magicamun/EnvNode/hardware/kicad/Sensors/SCT013Head/Lumberg_1503_09_Footprint.md

# Lumberg 1503 09 – SensorHead-Footprint

Quelle: https://cdn-reichelt.de/documents/datenblatt/C160/DS_1503_09.pdf (03/2007).
Draufsicht auf F.Cu, Stecköffnung nach -Y. Ursprung: Pad 1.
Das Hersteller-Bohrbild zeigt die Lötseite; X wurde für die Draufsicht gespiegelt.

| Pad | Funktion | X mm | Y mm | Langloch X × Y mm |
|---|---|---:|---:|---|
| 1 | Sleeve | 0 | 0 | 1,5 × 0,8 |
| 2 | Ring | -4,55 | 3,10 | 0,8 × 1,5 |
| 3 | Tip | 5,05 | 7,80 | 0,8 × 1,5 |
| 4 | Ring-Schaltkontakt (NC zu 2) | -4,00 | 11,00 | 1,5 × 0,8 |
| 5 | Tip-Schaltkontakt (NC zu 3) | 2,65 | 6,40 | 0,8 × 1,5 |

Durchkontaktierte Langlöcher gemäß Datenblatt, umlaufend 0,45 mm Kupferring.
Gehäuse 11,5 × 14,1 mm; Gewindehals nominell 3,5 mm lang und 6 mm Durchmesser.
F.Fab zeigt die nominelle Geometrie; F.CrtYd enthält 0,5 mm Reserve.
Keine Gehäusebohrung und kein Platinenkantenausschnitt werden automatisch erzeugt.
Kein 3D-Modell enthalten. Mutter/Freigängigkeit separat in der Gehäusekonstruktion berücksichtigen.
Vor Fertigung mechanische Passprobe mit Originalteil empfohlen.

Die Padnummern entsprechen dem Hersteller, nicht automatisch einem generischen KiCad-Audiosymbol.
Beim Symbol die Zuordnung 1=S, 2=R, 3=T, 4=RN, 5=TN beachten.
Den bestehenden zweipoligen J1 nicht ohne passende Pinzuordnung mit diesem fünfpoligen Footprint verknüpfen.
