magicamun/EnvNode/docs/site/sensors/sct013.md

# SCT013 und SCT013Head

!!! note "Entwicklungsstand / WIP"
    Der SCT013Head ist eine passive Aufbereitung für einen Stromwandler mit
    Spannungsausgang. Ein SCT013-Treiber ist in der gemeinsamen Firmware noch
    nicht registriert. Diese Seite ist keine fertige Aufbau- oder Kalibrieranleitung.

## Aufgabe und unterstützter Sensortyp

Der Head nimmt das Wechselspannungssignal eines SCT013 mit integrierter Bürde
und Spannungsausgang auf und verschiebt es in den positiven Messbereich des ESP32-ADC.
Die genaue SCT013-Ausführung, Nennstrom und Ausgangsspannung müssen zum Aufbau passen.
SCT013-Varianten mit reinem Stromausgang sind durch diesen Entwurf nicht abgedeckt.

Die kompakte Platine wird von einer verschraubten Lumberg-1503-09-Buchse getragen.
Das Pigtail zum Mainboard benötigt eine eigene Zugentlastung.

## Anschluss zum Mainboard

| Pin | Funktion |
| --- | --- |
| 1 | GND |
| 2 | Nicht verwendet; die angebotenen 5 V werden nicht genutzt |
| 3 | Aufbereitetes ADC-Signal |
| 4 | +3V3_SYS |

Das passt zur vierpoligen ADC-Portbelegung von Mini und Weather.
Verwende einen analogen Eingang und prüfe die tatsächliche Verdrahtung.

## Signalaufbereitung

Die aktuelle Entwurfsbeschreibung nennt R1 = R4 = 10 kΩ als Teiler relativ zur
Vorspannung VBIAS. R2/R3 bilden die Vorspannung aus der 3,3-V-Versorgung;
C2 stabilisiert sie. C1 = 10 nF liegt parallel zu R4.
Tip der Sensorbuchse führt über R1 zum ADC, Sleeve liegt an VBIAS.

Die Auslegung muss zum konkreten Spannungsausgang passen. Die Unterlagen enthalten
verschiedene Sensor-Ausgangspunkte; daraus ergibt sich keine universelle Stromkalibrierung.
Eine garantierte Überstromfestigkeit oder Schutzbeschaltung ist nicht nachgewiesen.

## Was vor einer Aufbauanleitung fehlt

- Konkrete SCT013-Ausführung und deren Ausgangsdaten festlegen.
- R1 in der Teileliste abgleichen: Der aktuelle Entwurf nennt 10 kΩ,
  der dokumentierte Artikelstand führt noch 1 kΩ.
- Schaltplan-/PCB-Zuordnung des ADC-Anschlusses und Bestückungsdruck abschließen.
- Buchse, Gehäusewand, Stecker und Zugentlastung mechanisch prüfen.
- Signalgrenzen, ADC-Abtastung, RMS-Auswertung und Kalibrierung am realen Aufbau prüfen.

Es gibt derzeit keine freigegebene PDF-Aufbauanleitung für den SCT013Head.
Historische Prüfnotizen mit widersprüchlichen Zwischenständen werden hier nicht
als aktuelle Fertigungsfreigabe übernommen.
