magicamun/EnvNode/docs/site/modules/index.md

# Erweiterungsmodule

Zum ersten Dokumentationsumfang gehören zwei Module:

| Modul | Aufgabe | Dokumentierter Stand |
| --- | --- | --- |
| [AnalogHydroPressure](analog-hydro-pressure/index.md) | Analoger Drucksensoranschluss und lokale 5-V-auf-24-V-Versorgung | Revision 0.5 |
| [DuoRelay](duo-relay/index.md) | Zwei über AUX_GPIO gesteuerte 5-V-Wechslerrelais | Revision 0.3 |

Die Produktseiten enthalten Verdrahtung, Bestückung, Inbetriebnahme und PDF-Anleitungen.
Wähle den Modulslot und die Firmware-Konfiguration passend zur tatsächlichen Hardware.
Die optionale EEPROM-Identifikation allein aktiviert keinen Modultreiber.
