magicamun/EnvNode/docs/site/kits/index.md

# Bausätze und Aufbau

Für den ersten Aufbau beginnt die Dokumentation mit [EnvNode Mini](../mainboards/mini/index.md).
Die revisionsbezogene Bestückungs- und Bring-up-Anleitung enthält die detaillierten
Montage- und Prüfabläufe.

## Sinnvolle Reihenfolge

1. Platinenrevision und dazugehörige Anleitung abgleichen.
2. Mainboard und Versorgungsbaustein nach Anleitung bestücken und prüfen.
3. Versorgung ohne Sensoren und Erweiterungsmodule kontrollieren.
4. Firmware und Boardprofil prüfen.
5. Einen unterstützten I²C-Sensor anschließen und eine erste Messung prüfen.
6. MQTT einrichten; weitere Module einzeln ergänzen.

Konkrete Kit-Lieferumfänge und Artikelzuordnungen werden erst nach Abgleich mit der
Teileliste ergänzt.
