magicamun/EnvNode/docs/site/mainboards/index.md

# Mainboards und Versorgung

| Baustein | Einordnung | Dokumentierter Stand |
| --- | --- | --- |
| [EnvNode Mini](mini/index.md) | Kompaktes Mainboard mit zwei Modulslots | Revision 0.8 |
| [EnvNode Weather / Weatherstation](weatherstation/index.md) | Mainboard mit einem Modulslot und zusätzlichen direkten Anschlüssen | Revision 0.2 |
| [ORing Power](oring-power/index.md) | Aufgelöteter Versorgungsbaustein für Mainboards | Anleitung 0.1; keine formale PCB-Revision |

Die Produktseiten enthalten Anschlüsse, Versorgung, Bestückung und erste Inbetriebnahme
sowie die zugehörigen PDF-Anleitungen. Revisionsangaben beziehen sich auf die
vorhandenen Unterlagen; gleiche sie mit deiner eingesetzten Platine ab.
