magicamun/EnvNode/hardware/kicad/Modules/FullSize/DuoRelay/Documentation/DuoRelay_Bestueckungs_und_Bringup_Rev0.2.pdf

ENVNODE · DUORELAY REV. 0.2

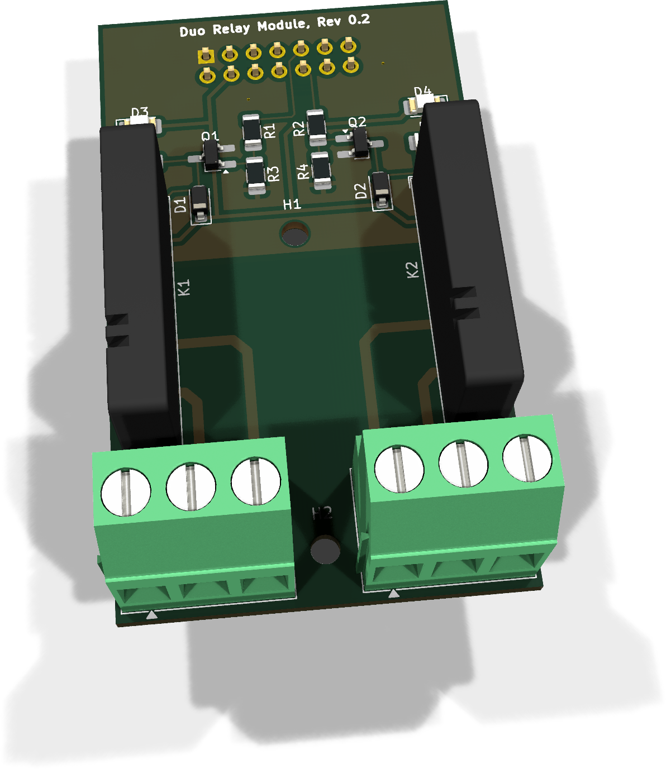
[picture p26: figure]

Bestückungs- und Bring-up-Anleitung · Entwurf · 1

ENVNODE DUORELAY

# Bestückungs- und Bring-up-Anleitung

FullSize-Modul Revision 0.2 · Erster Entwurf · PCB-Arbeitsstand 2. September 2026

Geltungsbereich: Diese Anleitung gilt für den aktuellen KiCad-Arbeitsstand des DuoRelay FullSize-Moduls und die Zuordnung im EnvNode-Artikelstamm. Sie beschreibt Handbestückung, Sichtprüfung und Erstinbetriebnahme mit Kleinspannung.

Dokumentstand: 2. September 2026

# 1. Teile und Vorbereitung

### 1.1 Elektronische Bestückung

Ref. | Anz. | Value / elektrische Daten | EnvNode-Part | Gehäuse / Footprint
D1, D2 | 2 | 1N4148W Freilaufdiode | ENP-00033 | SOD-123
D3, D4 | 2 | LED rot, KP-3216SURC | ENP-00064 | 1206 / 3216 Metric
R1, R2 | 2 | 1 kΩ, 1 %, 250 mW | ENP-00036 | 1206 / 3216 Metric
R3, R4 | 2 | 100 kΩ, 0,1 %, 250 mW | ENP-00016 | 1206 / 3216 Metric
R5, R6 | 2 | 1,5 kΩ, 1 %, 250 mW | ENP-00065 | 1206 / 3216 Metric
Q1, Q2 | 2 | BC817 NPN | ENP-00035 | SOT-23 Handsoldering
K1, K2 | 2 | Finder 34.51, 5-V-Spule, 1 Wechsler | ENP-00023 | Relay SPDT Finder 34.51
J3, J4 | 2 | Schraubklemme 1x3, 5,08 mm | ENP-00034 | Phoenix MKDS-3 horizontal
J1 | 1 | Stiftleiste 2x7, Bottom-Mount | ENP-00059 | EnvNode Bottom-Footprint
U1 | 1 | 24AA025E64T-I/OT Identifikations-EEPROM | ENP-00024 | SOT-23-6, derzeit DNP
C1 | 1 | 100 nF, X7R | ENP-00006 | 1206, derzeit DNP
PCB | 1 | DuoRelay FullSize Rev. 0.2 | ENP-00066 | 38,00 x 64,00 mm

DNP-Stand: U1 und C1 sind im aktuellen Kit als nicht zu bestücken geführt. Die Relaisfunktion arbeitet ohne EEPROM. Für spätere automatische Modulerkennung können beide Positionen nach Freigabe bestückt und U1 provisioniert werden.

### 1.2 Orientierung und Sicherheit

□ D1/D2: Kathodenmarkierung am Bauteil mit dem PCB-Aufdruck abgleichen.

□ D3/D4: LED-Polarität anhand Pin-1-/Kathodenmarkierung kontrollieren.

□ Q1/Q2: SOT-23-Lage und Pin-1-Markierung nicht spiegeln.

□ J1 wird von der Modulunterseite bestückt. Pin 1 ist am Footprint und am quadratischen Pad erkennbar.

□ K1/K2 und J3/J4 müssen plan aufliegen; erst einen Pin fixieren, Lage korrigieren, danach vollständig löten.

□ H1/H2 sind 2,7-mm-Bohrungen für M2,5-Hardware. Abstandshalter dürfen keine Leiterbahnen oder Lötstellen berühren.

Sicherheitsgrenze: Die vorhandenen Abstände und Relaisdaten sind keine Freigabe für Netzspannung. Klemmen, Sicherung, Gehäuse, Berührungsschutz, Lastart, Verschmutzungsgrad und Produktnorm müssen für die konkrete Anwendung bewertet werden. Der erste Bring-up erfolgt ausschließlich mit sicherer Kleinspannung.

### 1.3 Benötigte Hilfsmittel

□ Feinlötkolben, geeignetes Lot und Flussmittel; Vergrößerung für SOT-23 und SOD-123.

□ Multimeter mit Widerstands-, Dioden- und Durchgangsmessung.

□ Strombegrenztes 5-V-Labornetzteil und zwei ungefährliche Kleinspannungs-Testlasten.

□ Geeignetes EnvNode-Mainboard oder Prüfvorrichtung für AUX_GPIO1 und AUX_GPIO2.

# 2. Bestückungsübersicht

Bestückungsseite: J1 liegt oben, die beiden Treiberkanäle sind spiegelbildlich aufgebaut. Kanal 1 befindet sich links mit Q1, D1, D3, K1 und J3; Kanal 2 rechts mit Q2, D2, D4, K2 und J4.

Die Kontaktbezeichnungen sind am unteren Rand aufgedruckt. Vor externer Verdrahtung NO, COM und NC zusätzlich mit der Durchgangsmessung verifizieren.

### 2.1 Unterseite und Modulstecker

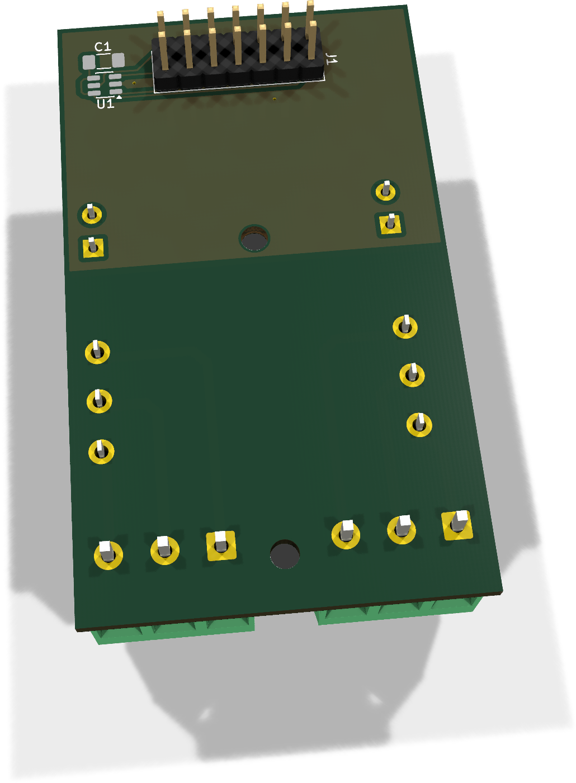
[picture p27: figure]

Unterseitenansicht: J1 sowie die optionalen Positionen U1/C1 liegen auf dieser Seite. Die Relais- und Klemmenanschlüsse erscheinen in der Ansicht gespiegelt.

Wichtig: J1 ist ein Bottom-Mount-Stecker. Nicht durch einen normalen, von oben bestückten 2x7-Header ersetzen; Pinreihenfolge und mechanische Einbaulage wären sonst falsch.

# 3. Empfohlene Löt-Reihenfolge

### 1. Widerstände

R1/R2 = 1 kΩ, R3/R4 = 100 kΩ und R5/R6 = 1,5 kΩ bestücken. Werte kanalweise gegenprüfen.

### 2. Dioden und LEDs

D1/D2 sowie D3/D4 polaritätsrichtig montieren. Nach jedem Kanal Diodentest durchführen.

### 3. Transistoren

Q1/Q2 ausrichten, zunächst einen Pin fixieren und anschließend alle Pins sauber benetzen.

### 4. Optional U1/C1

Im aktuellen Rev.-0.2-Kit DNP lassen. Nur gemeinsam und nach Freigabe der Identifikationsfunktion bestücken.

### 5. Bottom-Mount J1

Stecker von der Unterseite einsetzen. Mit einer Buchse oder Vorrichtung rechtwinklig halten und über Kreuz anlöten.

### 6. Relais K1/K2

Plan auf die Oberseite setzen. Zuerst je zwei weit auseinanderliegende Pins fixieren, Sitz prüfen, dann fertig löten.

### 7. Klemmen J3/J4

Öffnung nach außen ausrichten, plan auflegen und mechanisch belastbare THT-Lötstellen herstellen.

### 8. Reinigung und Sichtprüfung

Flussmittelreste entfernen, Kontaktbereich auf Fremdkörper prüfen und alle Lötstellen unter Vergrößerung abnehmen.

# 4. Anschlussbelegung

### 4.1 EnvNode-Modulstecker J1

Pin | Netz | Verwendung
1 | GND | Treiberreferenz
2 | +3V3_SYS | optional U1; A1 fest HIGH
3 | EEPROM_A0 | Slotabhängige U1-Adresse
4 | +5V | Relais- und LED-Versorgung
5 / 6 | I2C0_SDA / SCL | optional U1
7 / 8 | I2C1 | nicht verwendet
9 | AUX_GPIO1 | Relaiskanal 1
10 | AUX_GPIO2 | Relaiskanal 2
11-14 | SPI | nicht verwendet

Die Treibereingänge besitzen je 100 kΩ Pull-down. Beide Relais müssen während Reset, Boot und bei abgezogenem Controller sicher abgefallen bleiben.

### 4.2 Relaiskontakte J3/J4

Kanal | Klemme | Kontaktfolge laut Aufdruck
1 | J3 | NO - COM - NC
2 | J4 | NC - COM - NO

Die beiden Klemmen sind gegenüberliegend orientiert. Kontaktfolge daher nicht pauschal übertragen, sondern Aufdruck und Durchgangsmessung verwenden.

# 5. Prüfungen ohne Versorgung

□ Sichtprüfung aller Lötstellen, Leiterplattenkanten und Abstände bestanden.

□ Kein niederohmiger Kurzschluss zwischen +5 V und GND sowie zwischen +3V3_SYS und GND.

□ Q1/Q2 und D1/D2 in plausibler Diodenrichtung; keine Brücke an den SOT-23-Pins.

□ J1 von der Unterseite bestückt, Pin 1 korrekt, Stecker rechtwinklig und vollständig verlötet.

□ K1/K2 und J3/J4 plan aufliegend; keine kalten oder gerissenen THT-Lötstellen.

□ Relais im Ruhezustand: COM-NC niederohmig, COM-NO offen; beide Kanäle getrennt prüfen.

□ Zwischen Kontaktkreis und GND, +5 V, +3V3_SYS sowie GPIOs kein Durchgang.

□ U1/C1 entsprechend Fertigungsauftrag beide DNP oder beide freigegeben bestückt.

Bei jeder unerwarteten Verbindung zwischen Relaiskontaktseite und SELV-Steuerseite darf das Modul nicht eingeschaltet werden.

# 6. Erstinbetriebnahme

Schritt | Aktion / Erwartung
1 | Ohne externe Lasten und ausschließlich mit 5 V Kleinspannung starten. Strombegrenzung zunächst auf etwa 150 mA einstellen.
2 | Beide AUX_GPIO-Eingänge LOW halten. K1/K2 müssen abgefallen und D3/D4 aus sein.
3 | AUX_GPIO1 auf HIGH setzen: D3 leuchtet, K1 zieht hörbar an; AUX_GPIO2 bleibt aus.
4 | An J3 prüfen: COM-NO geschlossen, COM-NC offen. GPIO1 wieder LOW; Ruhezustand muss zurückkehren.
5 | AUX_GPIO2 entsprechend prüfen: D4, K2 und J4; Kanal 1 muss unbeeinflusst bleiben.
6 | Beide Kanäle kurz gleichzeitig einschalten; 5-V-Spannung und Stromaufnahme dokumentieren.

### 6.1 Funktions- und Belastungstest

□ Für die erste Kontaktprüfung nur eine berührungssichere Kleinspannungs-Testlast verwenden.

□ Jeden Kanal mindestens zehnmal schalten; LED, Relaisgeräusch und Kontaktzustand müssen konsistent sein.

□ Beide Kanäle gleichzeitig betätigen und Versorgungseinbruch am Modulstecker beobachten.

□ Kontaktwiderstand und Erwärmung bei der vorgesehenen Last gesondert qualifizieren.

□ Induktive, kapazitive und motorische Lasten benötigen eine anwendungsabhängige Schutzbeschaltung und Absicherung.

# 7. Messprotokoll

Prüfpunkt | Soll | Messwert | Bestanden | Bemerkung
+5 V am J1 | 4,75 bis 5,25 V
Ruhestrom, beide aus | dokumentieren
GPIO1 LOW / HIGH | K1 aus / ein
GPIO2 LOW / HIGH | K2 aus / ein
D3 / D4 | folgen K1 / K2
J3 Ruhe / aktiv | NC / NO korrekt
J4 Ruhe / aktiv | NC / NO korrekt
Beide Relais aktiv | 5 V stabil
Isolation Kontakt/SELV | kein Durchgang

# 8. Fehlerbilder

Beobachtung | Zuerst prüfen
Relais bleibt aus | +5 V an J1, AUX_GPIO-Pegel, R1/R2, Q1/Q2, Spule K1/K2 und Freilaufdiode.
LED leuchtet, Relais schaltet nicht | 5-V-Spannung unter Last, Spulenanschlüsse, Relais-Lötstellen und Spulenwiderstand.
Relais zieht beim Booten an | 100-kΩ-Pull-down R3/R4, GPIO-Konfiguration und Pinbelegung des verwendeten Slots.
Kontaktzustand vertauscht | Klemmenorientierung beachten: J3 und J4 tragen spiegelbildliche Aufdrucke; COM per Durchgang finden.
Hoher Strom / Erwärmung | Sofort ausschalten; D1/D2, Q1/Q2, Lötbrücken und Relais-Spulen prüfen.
Kanal beeinflusst den anderen | Gemeinsame 5-V-Versorgung, GPIO-Zuordnung, Lötbrücke zwischen den Treiberstufen.
U1 nicht erreichbar | Nur relevant, wenn bestückt: 3,3 V, I2C0, A0/A1, Orientierung, Adresse 0x52/0x53.

Fertigungsreife: Der elektrische und mechanische Stand ist für einen Rev.-0.2-Prototypenlauf plausibel. Vor Serien- oder Netzspannungsfreigabe fehlen weiterhin eine konkrete Klemmen-MPN, Lastqualifikation und anwendungsbezogene Sicherheitsbewertung.

# 9. Revisionsnachweis

Quelle | SHA-256
DuoRelay.kicad_pcb | 242f9711c18cf81b858417ce0f0d68c631eef2593229de874035f0864615322a
DuoRelay.kicad_sch | 8d009b299b0227dc91bdb96572533ef9922993829f7346a84a8630300917435b
DuoRelay.kicad_pro | 4a3a8a0ed6be982b91e17260304250d8a5bfeda32ea36c9a860300edd74c057f
README.md | a8fd0f2843a57bf01c0c8512cdc5afea1712142397578280fab4029cf7853337
EnvNode_Parts.xlsx | bca95cb81872b41eca7a18517cb41fc68700cc3a1cb6595b4e2c0744d4d927c3

Prüfbasis: PCB-Titelblock Rev. 0.2, Datum 2026-08-29. ERC am 2. September 2026: 0 Fehler und 9 dokumentierte Warnungen. Der KiCad-PCB-Stand und die Gerber-Daten waren bereits vorhanden; die fertigungsspezifische Freigabe bleibt Aufgabe des jeweiligen Auftrags.
