magicamun/EnvNode/hardware/kicad/Sensors/RainDetectorHead/RainDetectorHead.kicad_pcb

## KiCad design hardware/kicad/Sensors/RainDetectorHead/RainDetectorHead.kicad_pcb (2026-09-15)

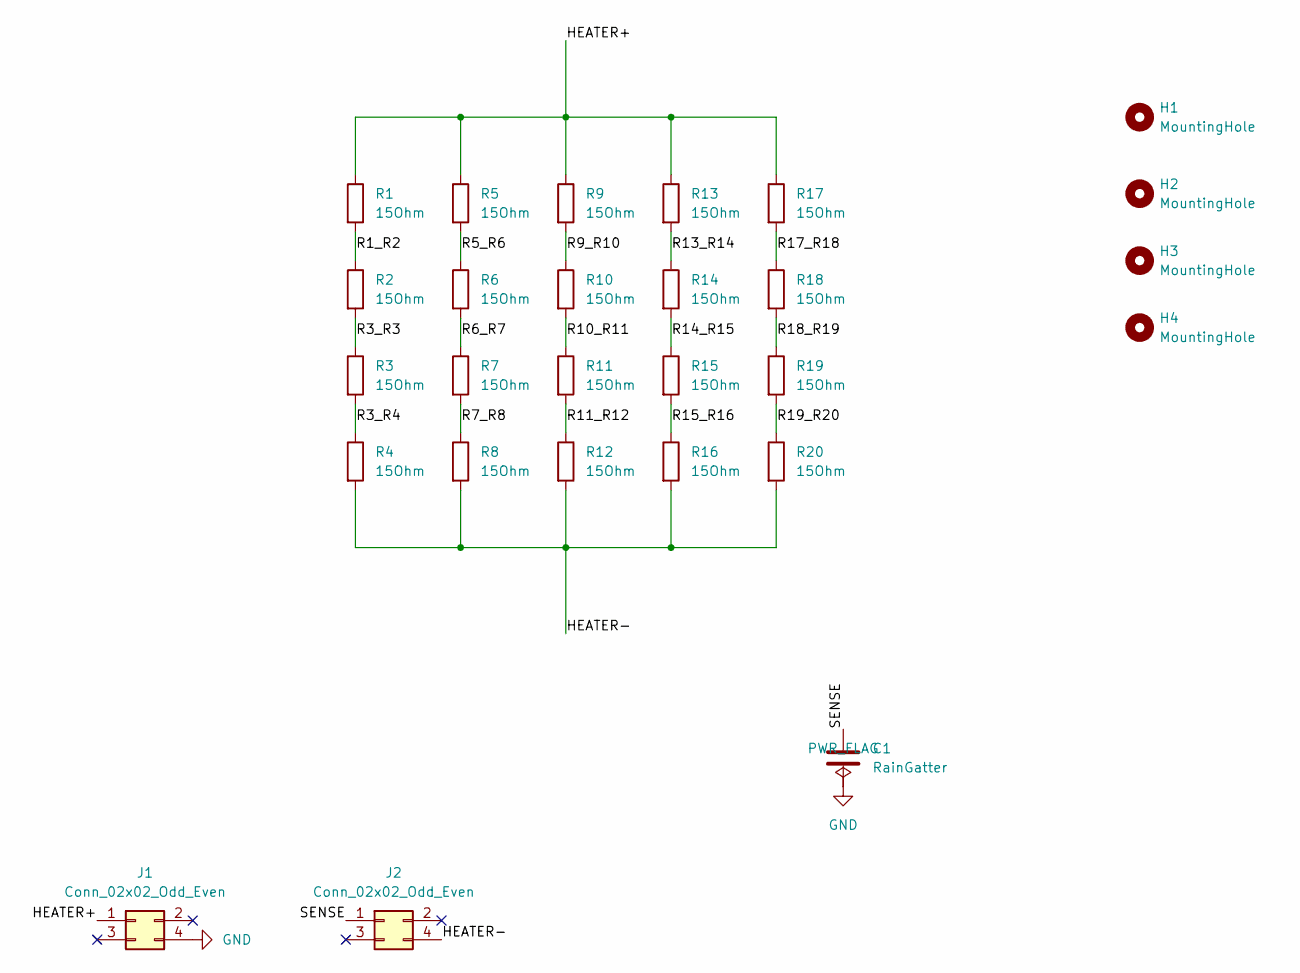
[picture p57: schematic RainDetectorHead.kicad_sch]

Parts:
C1: RainGatter; RainDetector_Interdigitated_48.86x37.25mm_P0.51mm
H1, H2, H3, H4: MountingHole; MountingHole_3.2mm_M3
J1, J2: Conn_02x02_Odd_Even; PinHeader_2x02_P2.54mm_Vertical_SMD
R1, R2, R3, R4, R5, R6, R7, R8, R9, R10, R11, R12, R13, R14, R15, R16, R17, R18, R19, R20: 15Ohm; R_1206_3216Metric_Pad1.30x1.75mm_HandSolder

Connections:
/HEATER+: J1.1, R1.1, R5.1, R9.1, R13.1, R17.1
/HEATER-: J2.4, R4.2, R8.2, R12.2, R16.2, R20.2
/R1_R2: R1.2, R2.1
/R3_R3: R2.2, R3.1
/R3_R4: R3.2, R4.1
/R5_R6: R5.2, R6.1
/R6_R7: R6.2, R7.1
/R7_R8: R7.2, R8.1
/R9_R10: R9.2, R10.1
/R10_R11: R10.2, R11.1
/R11_R12: R11.2, R12.1
/R13_R14: R13.2, R14.1
/R14_R15: R14.2, R15.1
/R15_R16: R15.2, R16.1
/R17_R18: R17.2, R18.1
/R18_R19: R18.2, R19.1
/R19_R20: R19.2, R20.1
/SENSE: C1.1, J2.1
GND: C1.2, J1.4

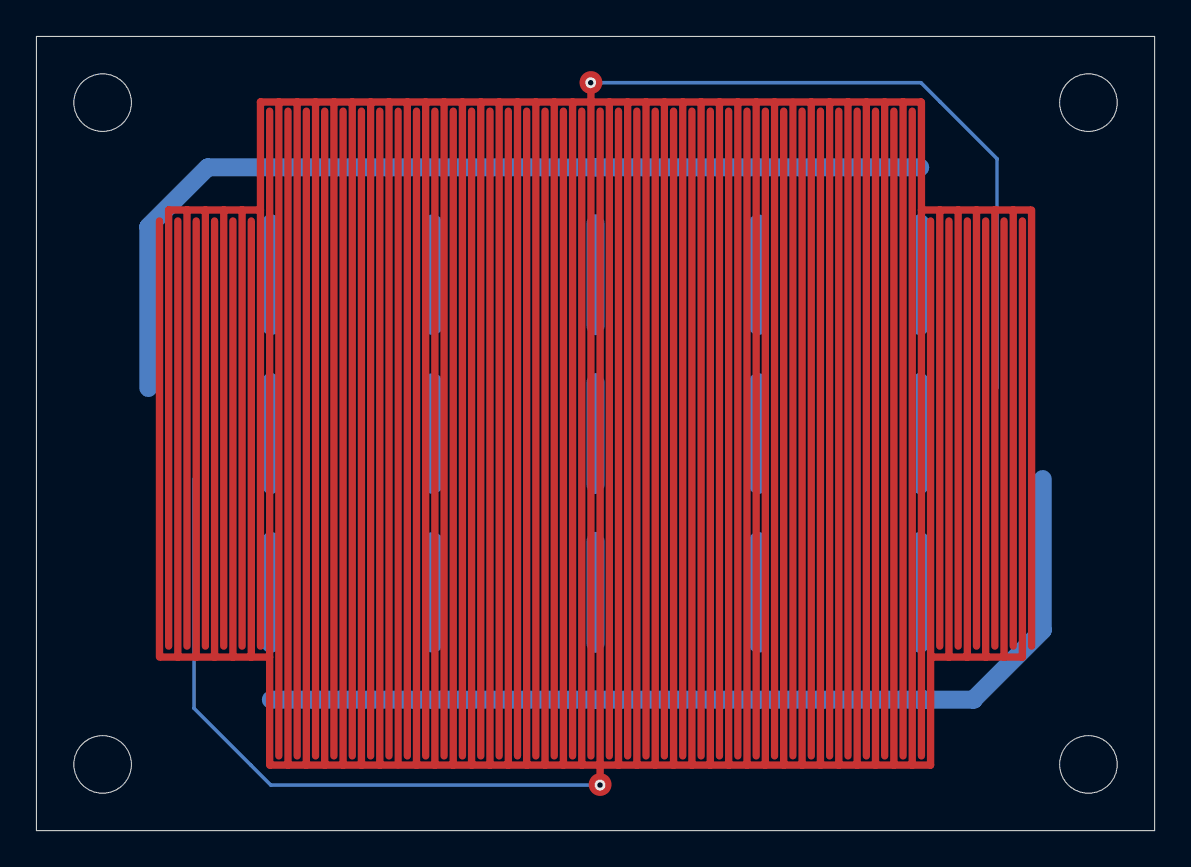
[picture p58: board RainDetectorHead.kicad_pcb from above]

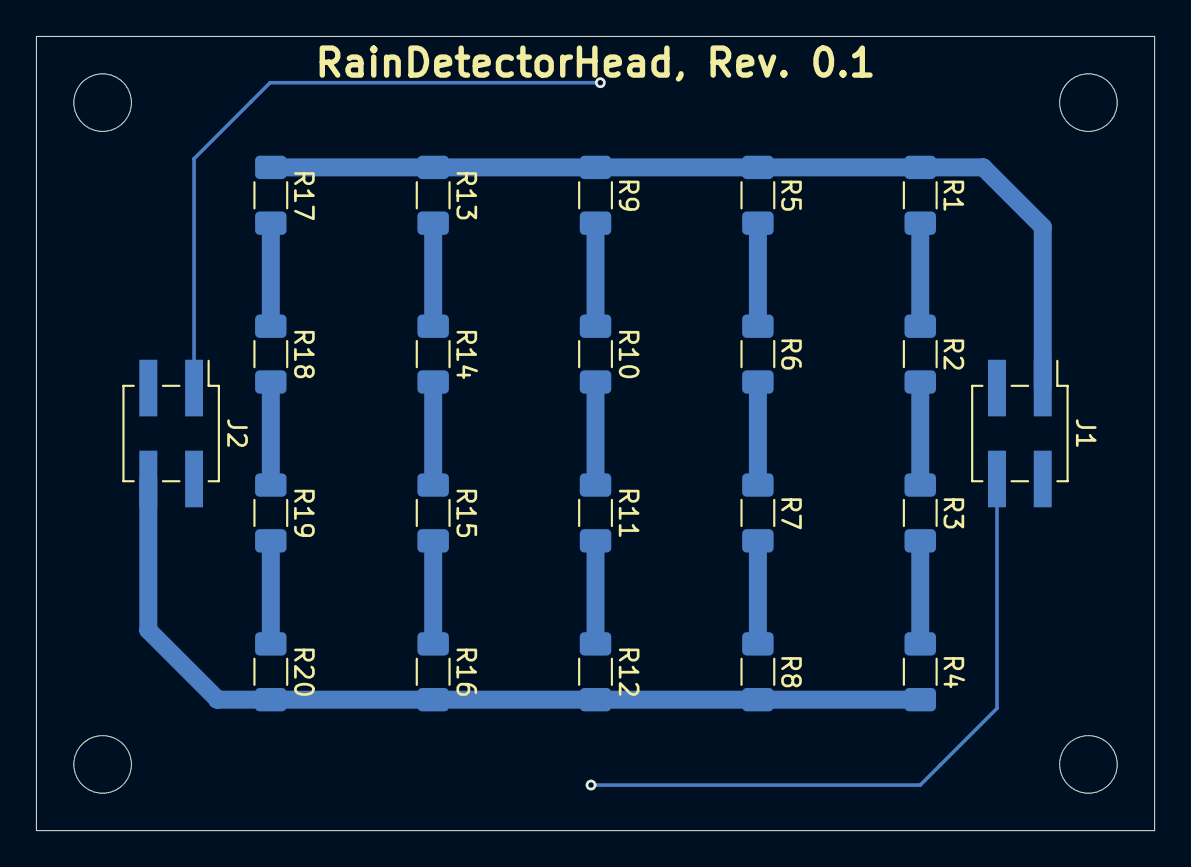
[picture p59: board RainDetectorHead.kicad_pcb from below]

Board: 2 copper layers, 62.1 x 44.1 mm, 27 parts (22 on the bottom side), 19 nets.
