magicamun/EnvNode/hardware/kicad/Sensors/RainDetectorController/RainDetectorController.kicad_pcb

## KiCad design hardware/kicad/Sensors/RainDetectorController/RainDetectorController.kicad_pcb (2026-09-15)

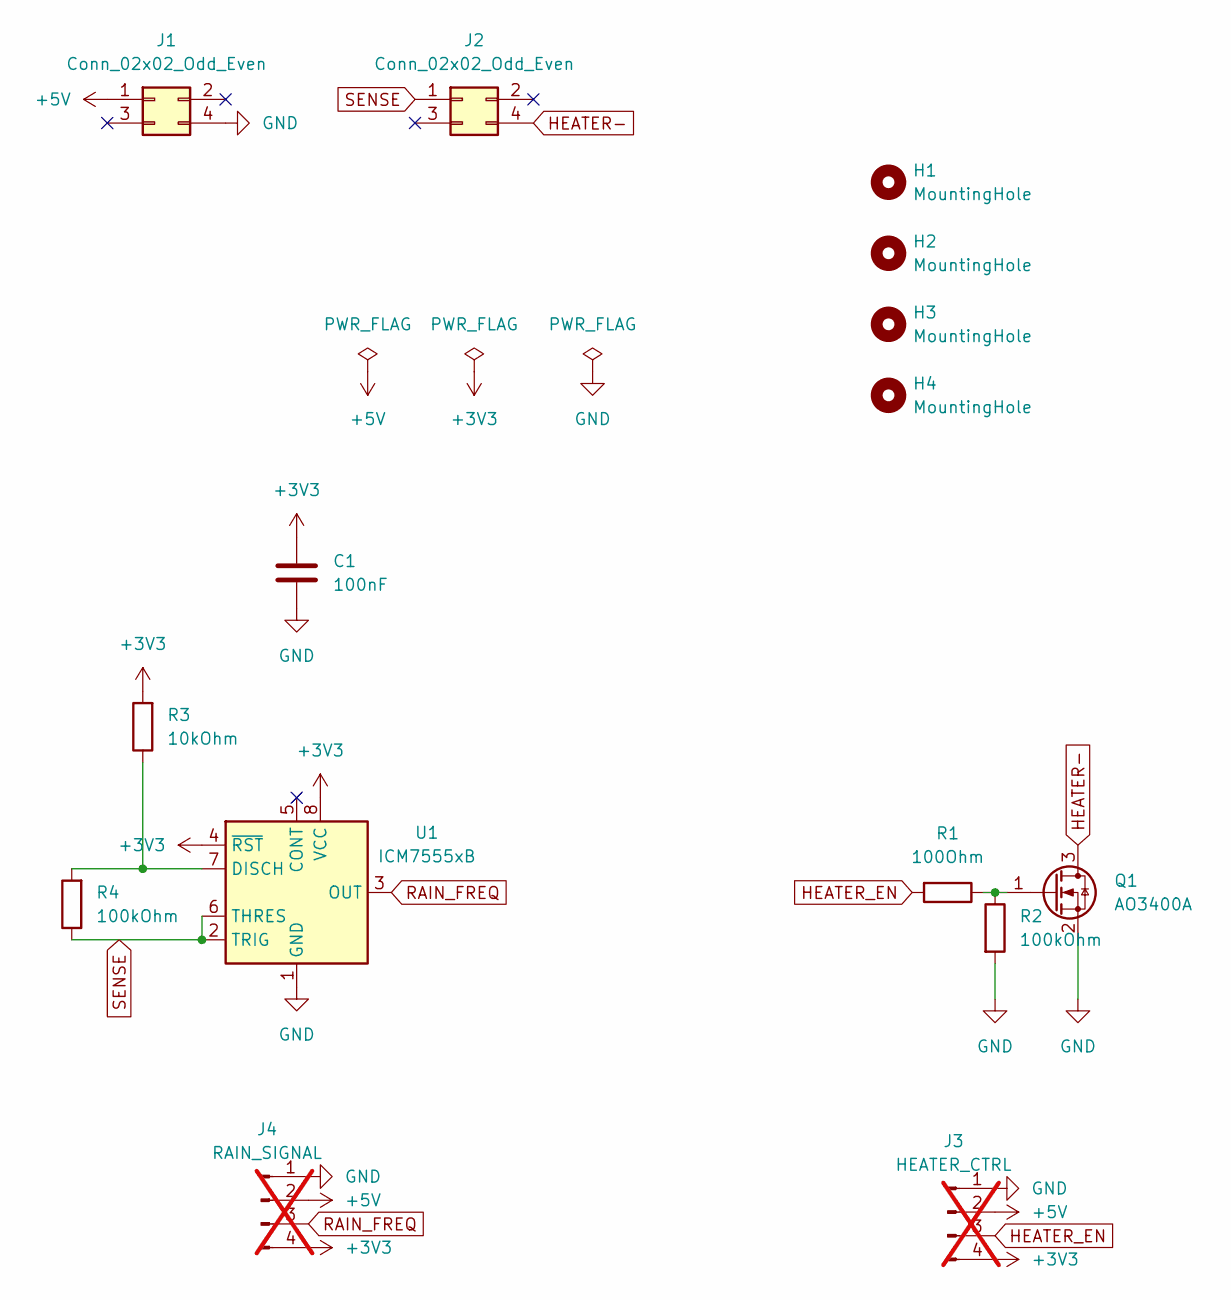
[picture p60: schematic RainDetectorController.kicad_sch]

Parts:
C1: 100nF; C_1206_3216Metric_Pad1.33x1.80mm_HandSolder
H1, H2, H3, H4: MountingHole; MountingHole_3.2mm_M3
J1, J2: Conn_02x02_Odd_Even; PinSocket_2x02_P2.54mm_Vertical
J3: HEATER_CTRL; PinHeader_1x04_P2.54mm_Vertical; not fitted
J4: RAIN_SIGNAL; PinHeader_1x04_P2.54mm_Vertical; not fitted
Q1: AO3400A; SOT-23
R1: 100Ohm; R_1206_3216Metric_Pad1.30x1.75mm_HandSolder
R2, R4: 100kOhm; R_1206_3216Metric_Pad1.30x1.75mm_HandSolder
R3: 10kOhm; R_1206_3216Metric_Pad1.30x1.75mm_HandSolder
U1: ICM7555xB; SOIC-8_3.9x4.9mm_P1.27mm

Connections:
+3V3: C1.1, J3.4, J4.4, R3.2, U1.4 (~RST), U1.8 (VCC)
+5V: J1.1, J3.2, J4.2
GND: C1.2, J1.4, J3.1, J4.1, Q1.2 (S), R2.2, U1.1 (GND)
HEATER-: J2.4, Q1.3 (D)
HEATER_EN: J3.3, R1.2
unnamed: Q1.1 (G), R1.1, R2.1
unnamed: R3.1, R4.2, U1.7 (DISCH)
RAIN_FREQ: J4.3, U1.3 (OUT)
SENSE: J2.1, R4.1, U1.2 (TRIG), U1.6 (THRES)

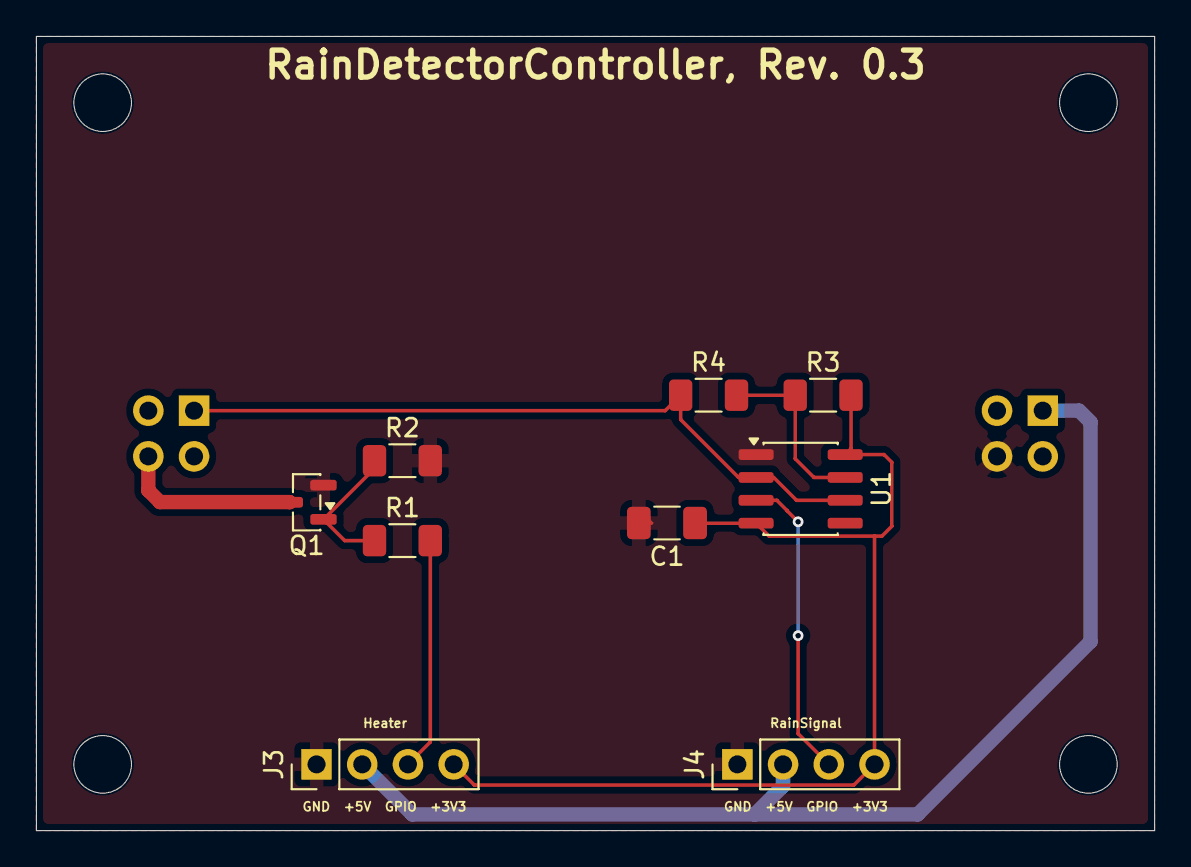
[picture p61: board RainDetectorController.kicad_pcb from above]

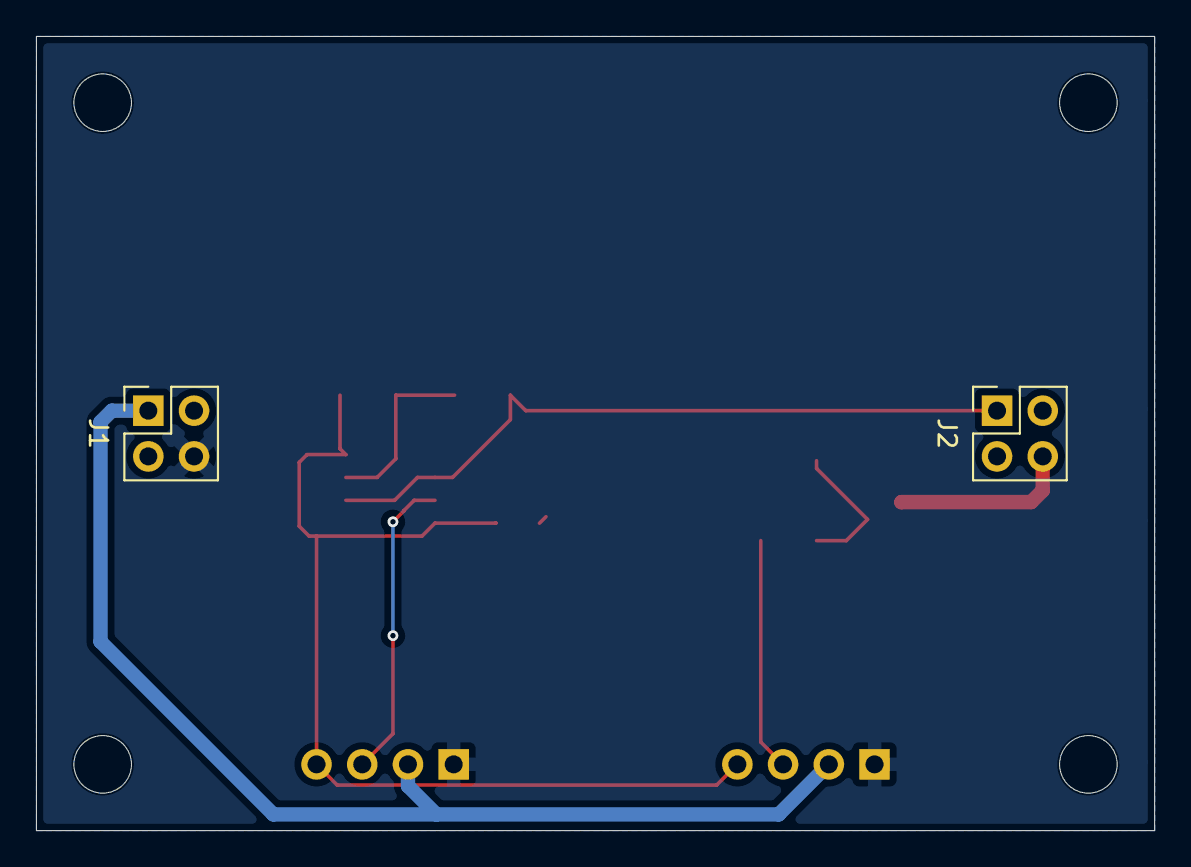
[picture p62: board RainDetectorController.kicad_pcb from below]

Board: 2 copper layers, 62.1 x 44.1 mm, 15 parts (2 on the bottom side), 9 nets.
