magicamun/EnvNode/hardware/kicad/Modules/HalfSize/I2C Carrier HalfSize/I2C Carrier HalfSize.kicad_pcb

## KiCad design hardware/kicad/Modules/HalfSize/I2C Carrier HalfSize/I2C Carrier HalfSize.kicad_pcb (2026-09-08)

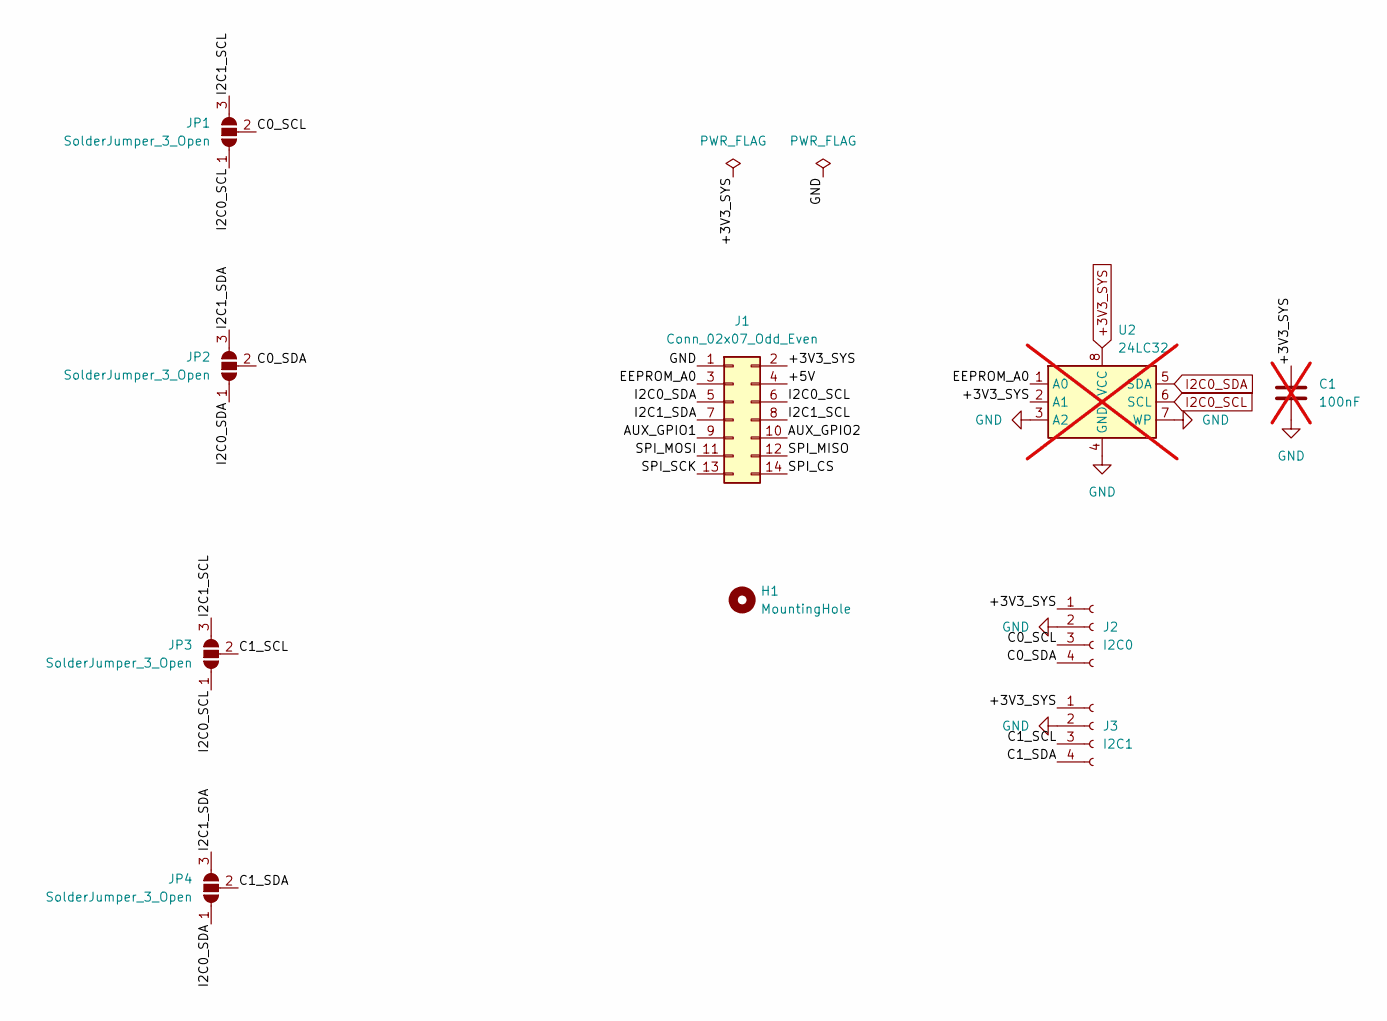
[picture p63: schematic I2C Carrier HalfSize.kicad_sch]

Parts:
C1: 100nF; C_1206_3216Metric_Pad1.33x1.80mm_HandSolder; not fitted
H1: MountingHole; MountingHole_2.7mm_M2.5_DIN965
J1: Conn_02x07_Odd_Even; PinHeader_2x07_P2.54mm_Vertical_Bottom
J2: I2C0; PinSocket_1x04_P2.54mm_Vertical
J3: I2C1; PinSocket_1x04_P2.54mm_Vertical
JP1, JP2, JP3, JP4: SolderJumper_3_Open; SolderJumper-3_P1.3mm_Open_RoundedPad1.0x1.5mm
U2: 24LC32; SOIC-8_3.9x4.9mm_P1.27mm; not fitted

Connections:
+3V3_SYS: C1.1, J1.2, J2.1, J3.1, U2.2 (A1), U2.8 (VCC)
/+5V: J1.4
/AUX_GPIO1: J1.9
/AUX_GPIO2: J1.10
/C0_SCL: J2.3, JP1.2 (C)
/C0_SDA: J2.4, JP2.2 (C)
/C1_SCL: J3.3, JP3.2 (C)
/C1_SDA: J3.4, JP4.2 (C)
/EEPROM_A0: J1.3, U2.1 (A0)
/I2C1_SCL: J1.8, JP1.3 (B), JP3.3 (B)
/I2C1_SDA: J1.7, JP2.3 (B), JP4.3 (B)
/SPI_CS: J1.14
/SPI_MISO: J1.12
/SPI_MOSI: J1.11
/SPI_SCK: J1.13
GND: C1.2, J1.1, J2.2, J3.2, U2.3 (A2), U2.4 (GND), U2.7 (WP)
I2C0_SCL: J1.6, JP1.1 (A), JP3.1 (A), U2.6 (SCL)
I2C0_SDA: J1.5, JP2.1 (A), JP4.1 (A), U2.5 (SDA)

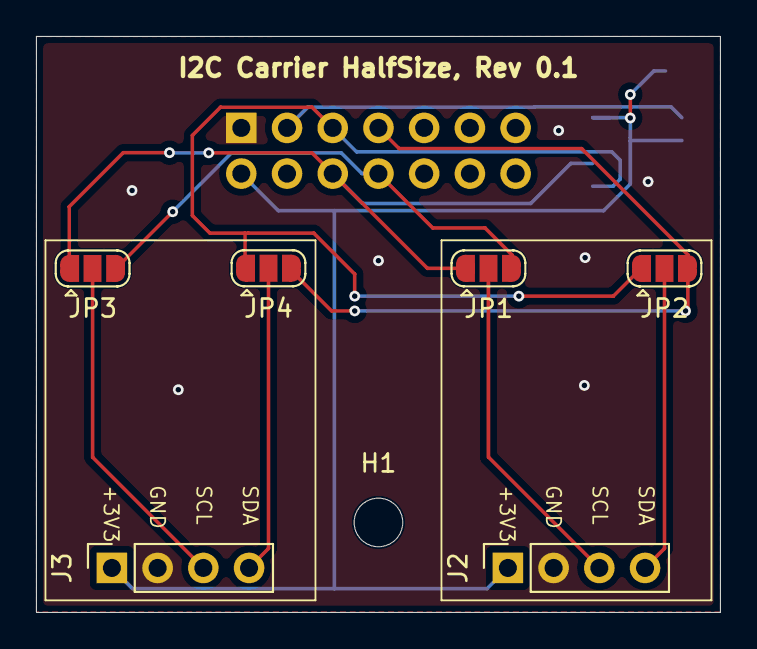
[picture p64: board I2C Carrier HalfSize.kicad_pcb from above]

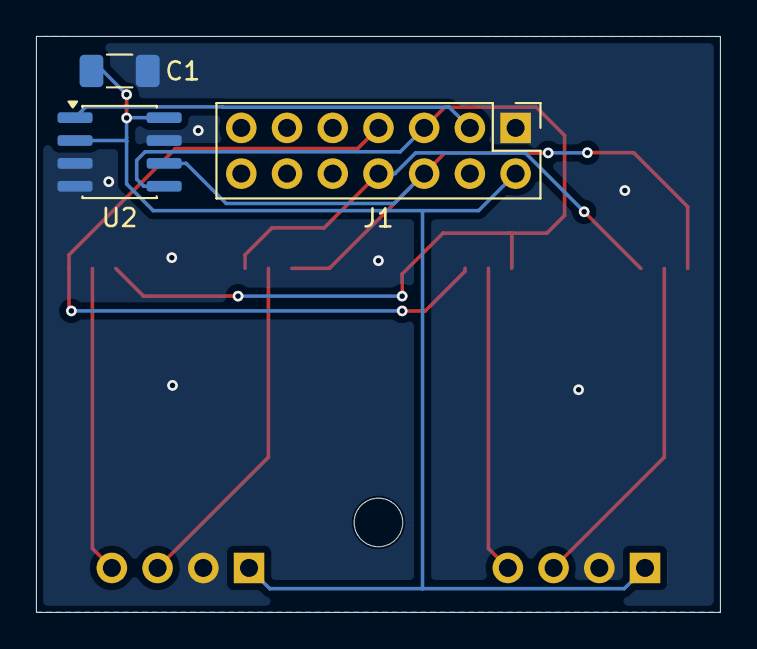
[picture p65: board I2C Carrier HalfSize.kicad_pcb from below]

Board: 2 copper layers, 38.0 x 32.0 mm, 10 parts (3 on the bottom side), 11 nets.
