magicamun/EnvNode/hardware/kicad/Modules/HalfSize/Empty-SMD/Empty-SMD.kicad_pcb

## KiCad design hardware/kicad/Modules/HalfSize/Empty-SMD/Empty-SMD.kicad_pcb (2026-09-06)

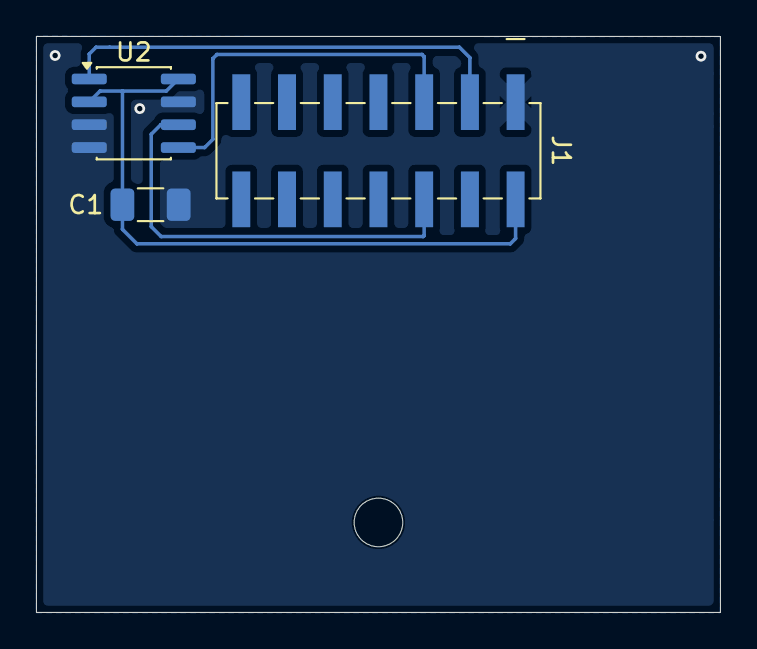
[picture p66: board Empty-SMD.kicad_pcb from below]

Board: 2 copper layers, 38.0 x 32.0 mm, 4 parts (3 on the bottom side), 5 nets.

Parts:
C1: 100nF; C_1206_3216Metric_Pad1.33x1.80mm_HandSolder
H1: MountingHole; MountingHole_2.7mm_M2.5_DIN965
J1: Conn_02x07_Odd_Even; J_Wurth_WR-PHD_61031421121
U2: 24LC32; SOIC-8_3.9x4.9mm_P1.27mm

Connections:
+3V3_SYS: C1.1, J1.2, U2.2 (A1), U2.8 (VCC)
/EEPROM_A0: J1.3, U2.1 (A0)
GND: C1.2, J1.1, U2.3 (A2), U2.4 (GND), U2.7 (WP)
I2C0_SCL: J1.6, U2.6 (SCL)
I2C0_SDA: J1.5, U2.5 (SDA)
