magicamun/EnvNode/hardware/kicad/Modules/FullSize/DuoRelay/DuoRelay.kicad_pcb

## KiCad design hardware/kicad/Modules/FullSize/DuoRelay/DuoRelay.kicad_pcb (2026-09-06)

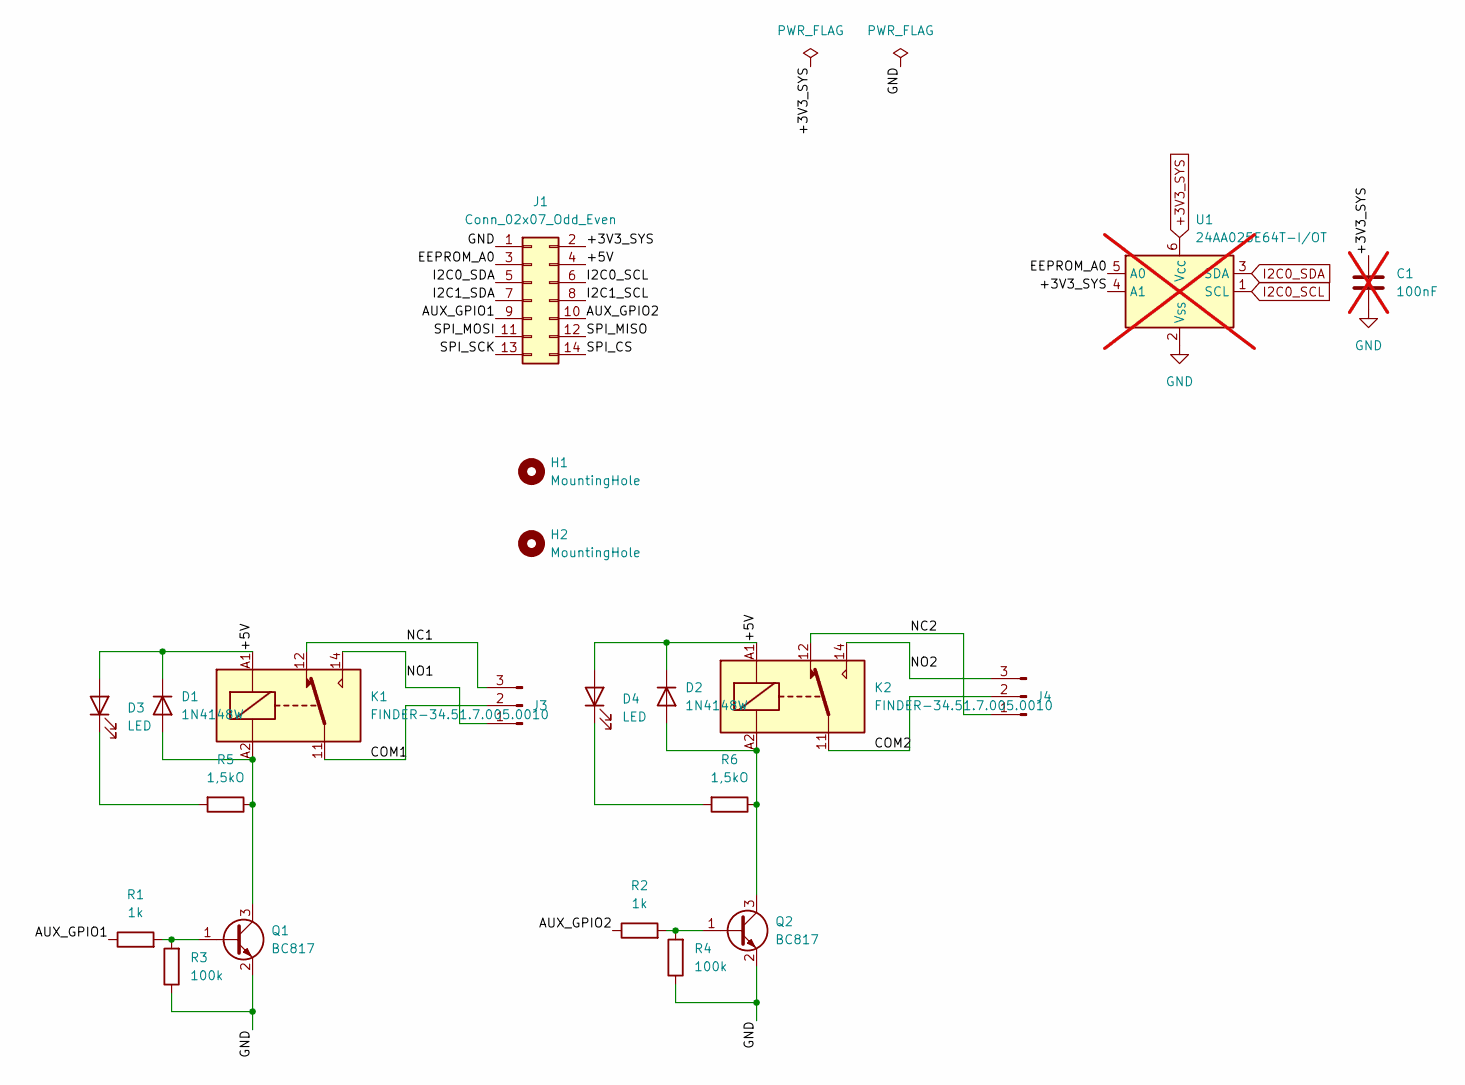
[picture p67: schematic DuoRelay.kicad_sch]

Parts:
C1: 100nF; C_1206_3216Metric_Pad1.33x1.80mm_HandSolder; not fitted
D1, D2: 1N4148W; D_SOD-123
D3, D4: LED; LED_1206_3216Metric_Pad1.42x1.75mm_HandSolder
H1, H2: MountingHole; MountingHole_2.7mm_M2.5_DIN965
J1: Conn_02x07_Odd_Even; PinHeader_2x07_P2.54mm_Vertical_Bottom
J3, J4: TerminalBlock_Phoenix_MKDS-3-3-5.08_1x03_P5.08mm_Horizontal
K1, K2: FINDER-34.51.7.005.0010; Relay_SPDT_Finder_34.51_Vertical
Q1, Q2: BC817; SOT-23_Handsoldering
R1, R2: 1k; R_1206_3216Metric_Pad1.30x1.75mm_HandSolder
R3, R4: 100k; R_1206_3216Metric_Pad1.30x1.75mm_HandSolder
R5, R6: 1,5kO; R_1206_3216Metric_Pad1.30x1.75mm_HandSolder
U1: 24AA025E64T-I/OT; SOT-23-6; not fitted

Connections:
+3V3_SYS: C1.1, J1.2, U1.4 (A1); also elsewhere on the board
/+5V: D1.1 (K), D2.1 (K), D3.2 (A), D4.2 (A), J1.4, K1.A1, K2.A1
/AUX_GPIO1: J1.9, R1.1
/AUX_GPIO2: J1.10, R2.1
/COM1: J3.2, K1.11
/COM2: J4.2, K2.11
/EEPROM_A0: J1.3, U1.5 (A0); also elsewhere on the board
/I2C1_SCL: J1.8
/I2C1_SDA: J1.7
/NC1: J3.3, K1.12
/NC2: J4.1, K2.12
/NO1: J3.1, K1.14
/NO2: J4.3, K2.14
/SPI_CS: J1.14
/SPI_MISO: J1.12
/SPI_MOSI: J1.11
/SPI_SCK: J1.13
GND: C1.2, J1.1, Q1.2 (E), Q2.2 (E), R3.1, R4.1, U1.2 (V_{SS}); also elsewhere on the board
I2C0_SCL: J1.6; also elsewhere on the board
I2C0_SDA: J1.5; also elsewhere on the board
unnamed: D1.2 (A), K1.A2, Q1.3 (C), R5.1
unnamed: D2.2 (A), K2.A2, Q2.3 (C), R6.1
unnamed: D3.1 (K), R5.2
unnamed: D4.1 (K), R6.2
unnamed: Q1.1 (B), R1.2, R3.2
unnamed: Q2.1 (B), R2.2, R4.2
