magicamun/EnvNode/hardware/kicad/Modules/FullSize/DuoRelay/DuoRelay.kicad_pcb

## KiCad design hardware/kicad/Modules/FullSize/DuoRelay/DuoRelay.kicad_pcb (continued)

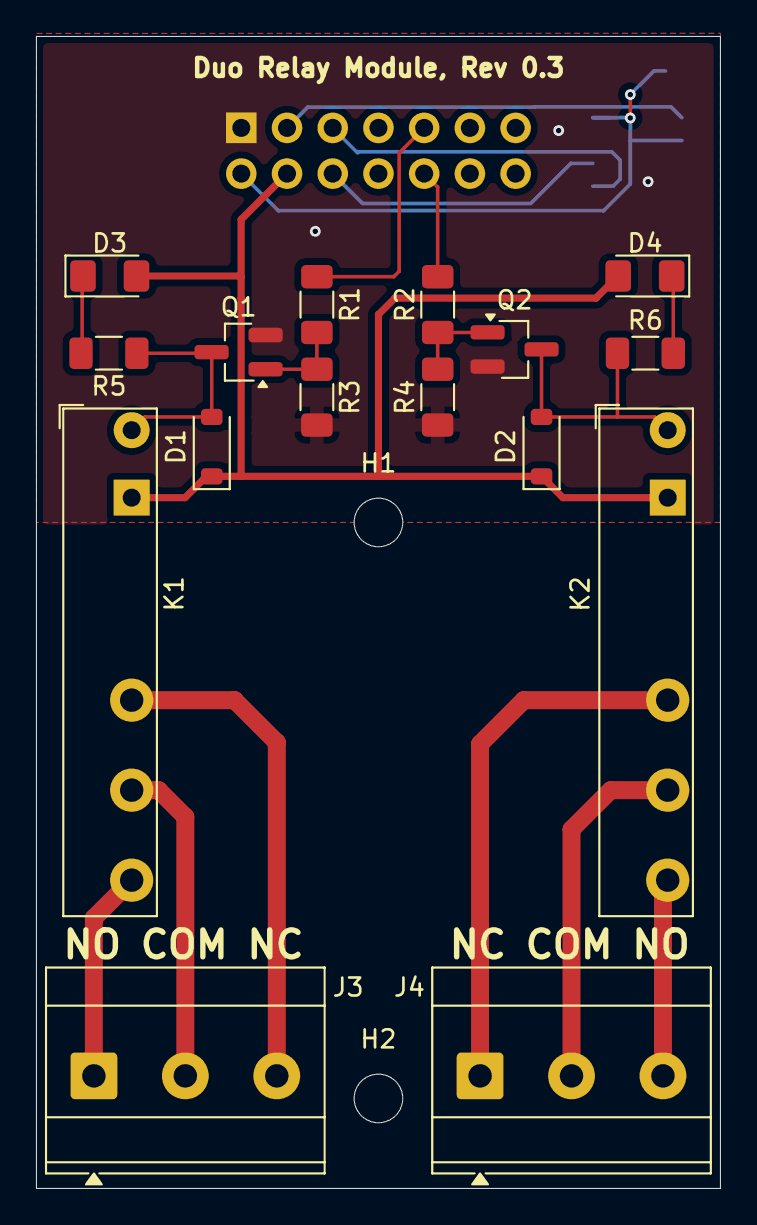
[picture p68: board DuoRelay.kicad_pcb from above]

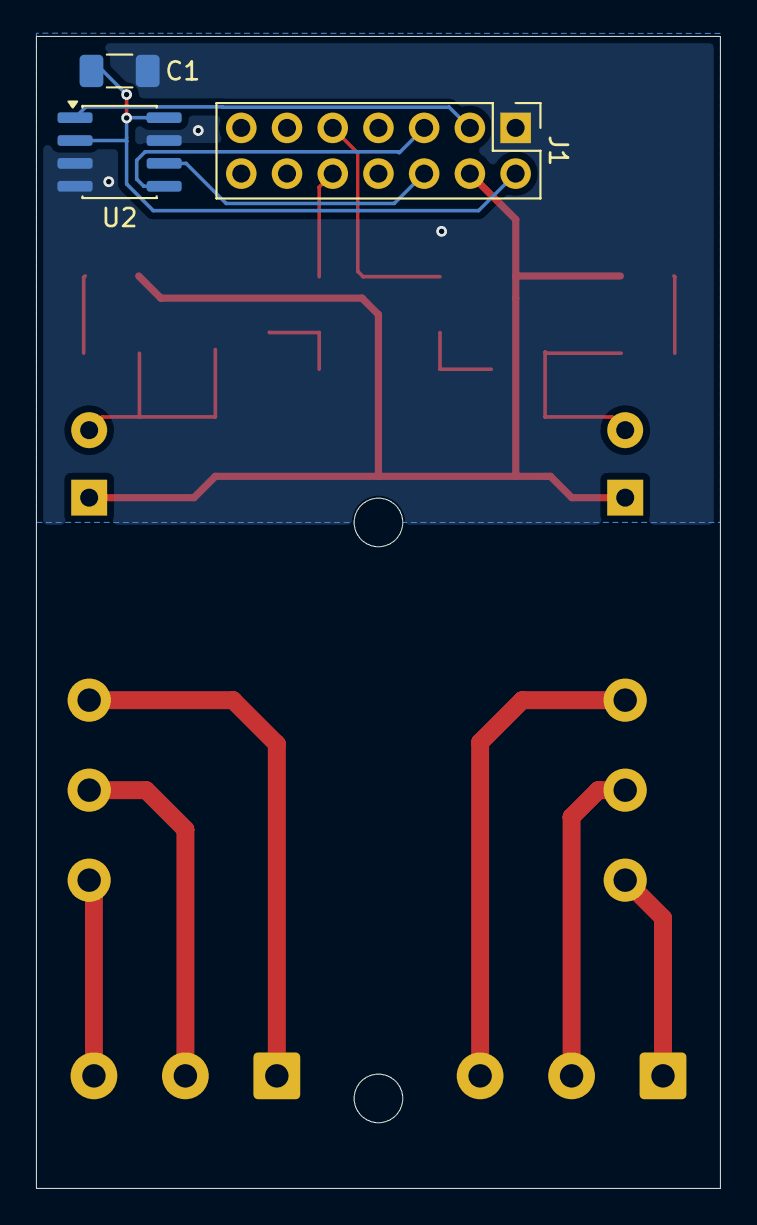
[picture p69: board DuoRelay.kicad_pcb from below]

Board: 2 copper layers, 38.0 x 64.0 mm, 21 parts (3 on the bottom side), 20 nets.

Other parts of the board:
U2: 24LC32; SOIC-8_3.9x4.9mm_P1.27mm

Their connections:
+3V3_SYS: U2.2 (A1), U2.8 (VCC); also elsewhere on the board
/EEPROM_A0: U2.1 (A0); also elsewhere on the board
GND: U2.3 (A2), U2.4 (GND), U2.7 (WP); also elsewhere on the board
I2C0_SCL: U2.6 (SCL); also elsewhere on the board
I2C0_SDA: U2.5 (SDA); also elsewhere on the board
