magicamun/EnvNode/hardware/kicad/Revision-0.1/MainBoards/EnvNode/EnvNode.kicad_pcb

## KiCad design hardware/kicad/Revision-0.1/MainBoards/EnvNode/EnvNode.kicad_pcb (2026-08-24)

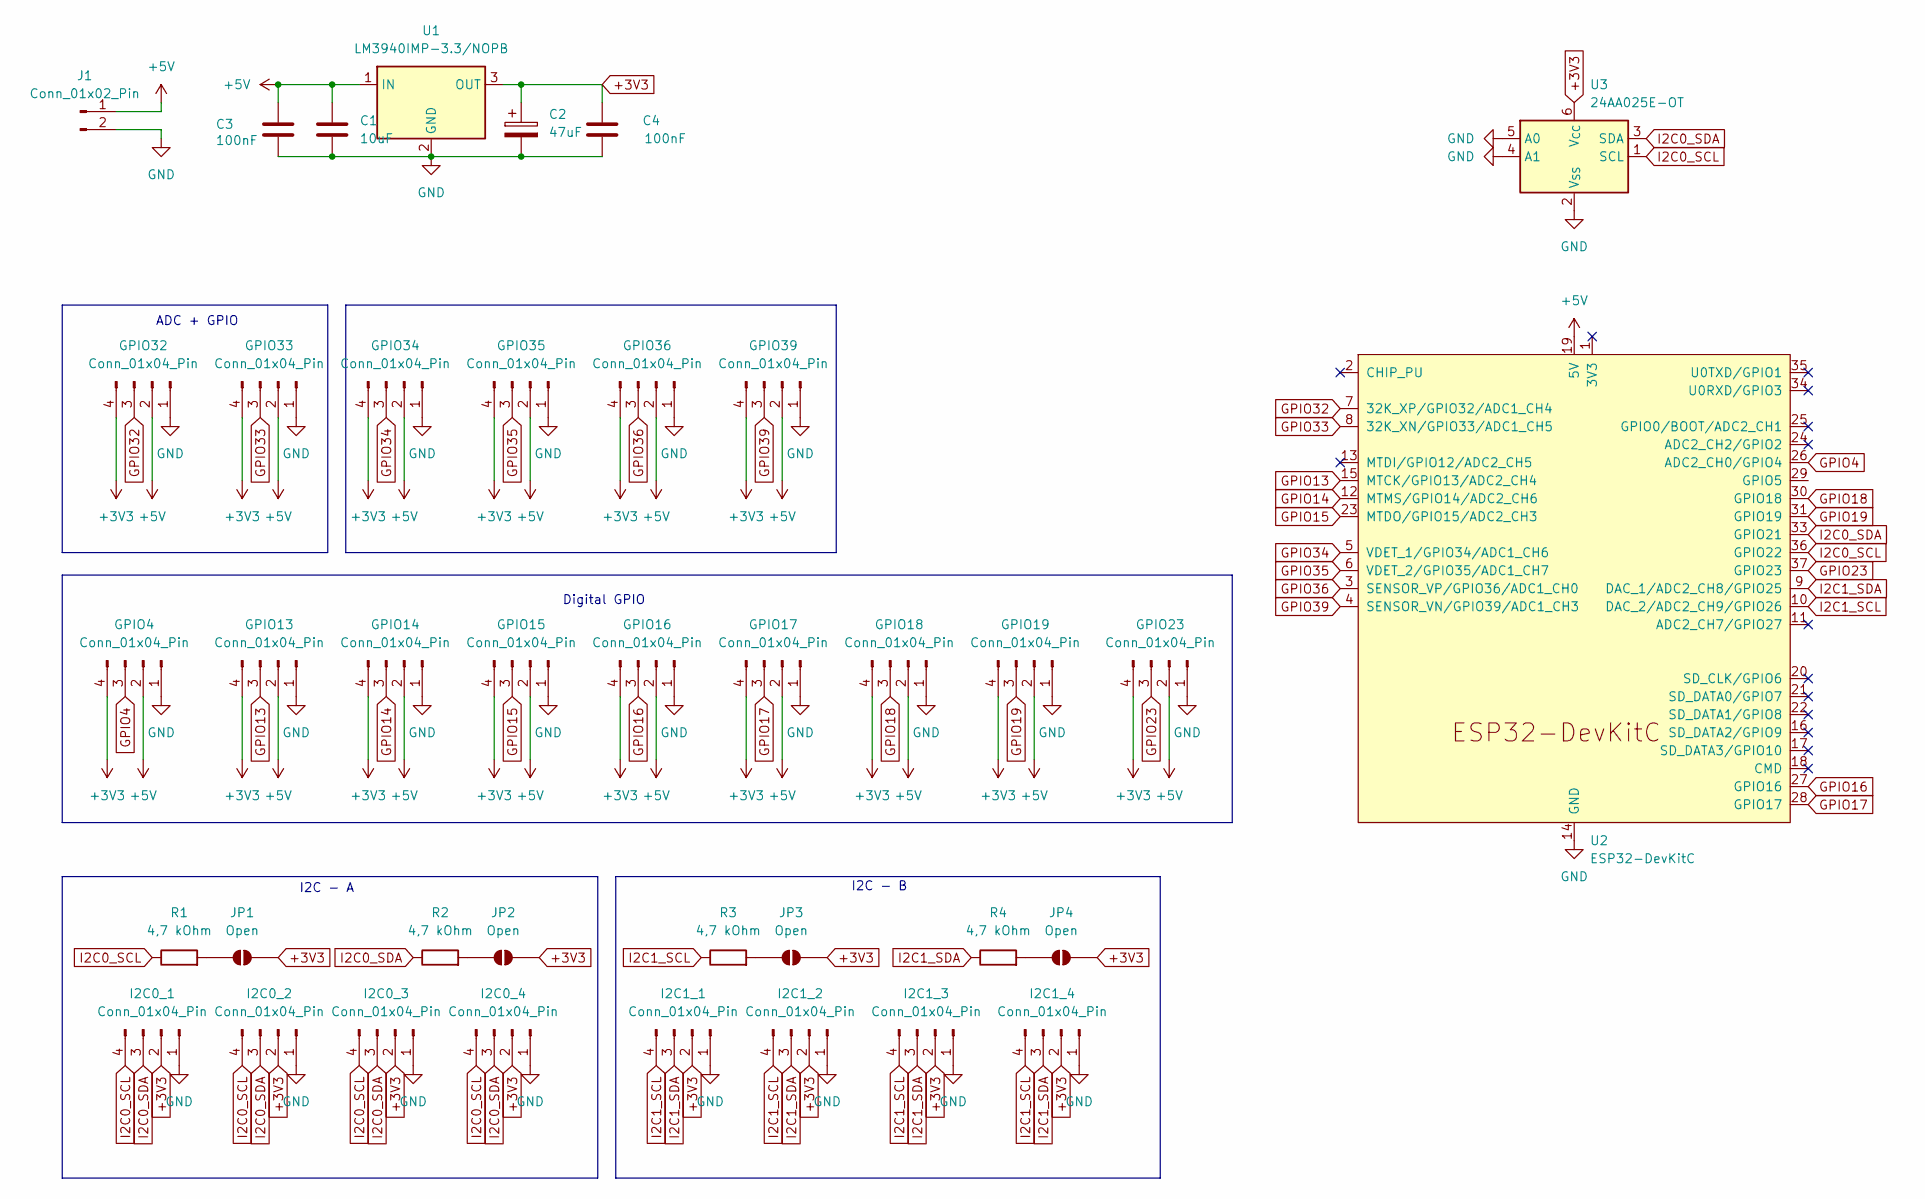
[picture p70: schematic EnvNode.kicad_sch, EnvNode]

Parts:
C1: 10uF; C_1206_3216Metric_Pad1.33x1.80mm_HandSolder
C2: 47uF; CP_EIA-3528-21_Kemet-B
C3, C4: 100nF; C_1206_3216Metric_Pad1.33x1.80mm_HandSolder
GPIO4, GPIO13, GPIO14, GPIO15, GPIO16, GPIO17, GPIO18, GPIO19, GPIO23, GPIO32, GPIO33, GPIO34, GPIO35, GPIO36, GPIO39: Conn_01x04_Pin; JST_PH_B4B-PH-K_1x04_P2.00mm_Vertical
I2C0_1, I2C0_2, I2C0_3, I2C1_1, I2C1_2, I2C1_3: Conn_01x04_Pin; JST_SH_SM04B-SRSS-TB_1x04-1MP_P1.00mm_Horizontal
I2C0_4, I2C1_4: Conn_01x04_Pin; QWIIC_PinSocket_1x04_P2.54mm_Vertical
J1: Conn_01x02_Pin; JST_PH_B2B-PH-K_1x02_P2.00mm_Vertical
JP1, JP2, JP3, JP4: Open; SolderJumper-2_P1.3mm_Open_Pad1.0x1.5mm
R1, R2, R3, R4: 4,7 kOhm; R_1206_3216Metric_Pad1.30x1.75mm_HandSolder
U1: LM3940IMP-3.3/NOPB; SOT-223-3_TabPin2
U2: ESP32-DevKitC
U3: 24AA025E-OT; SOT-23-6_Handsoldering

Connections:
+3V3: C2.1, C4.2, GPIO4.4, GPIO13.4, GPIO14.4, GPIO15.4, GPIO16.4, GPIO17.4, GPIO18.4, GPIO19.4, GPIO23.4, GPIO32.4, GPIO33.4, GPIO34.4, GPIO35.4, GPIO36.4, GPIO39.4, I2C0_1.2, I2C0_2.2, I2C0_3.2, I2C0_4.2, I2C1_1.2, I2C1_2.2, I2C1_3.2, I2C1_4.2, JP1.2 (B), JP2.2 (B), JP3.2 (B), JP4.2 (B), U1.3 (OUT), U3.6 (V_{CC})
+5V: C1.1, C3.2, GPIO4.2, GPIO13.2, GPIO14.2, GPIO15.2, GPIO16.2, GPIO17.2, GPIO18.2, GPIO19.2, GPIO23.2, GPIO32.2, GPIO33.2, GPIO34.2, GPIO35.2, GPIO36.2, GPIO39.2, J1.1, U1.1 (IN), U2.19 (5V)
GND: C1.2, C2.2, C3.1, C4.1, GPIO4.1, GPIO13.1, GPIO14.1, GPIO15.1, GPIO16.1, GPIO17.1, GPIO18.1, GPIO19.1, GPIO23.1, GPIO32.1, GPIO33.1, GPIO34.1, GPIO35.1, GPIO36.1, GPIO39.1, I2C0_1.1, I2C0_2.1, I2C0_3.1, I2C0_4.1, I2C1_1.1, I2C1_2.1, I2C1_3.1, I2C1_4.1, J1.2, U1.2 (GND), U2.14 (GND), U2.32 (GND), U2.38 (GND), U3.2 (V_{SS}), U3.4 (A1), U3.5 (A0)
GPIO4: GPIO4.3, U2.26 (ADC2_CH0/GPIO4)
GPIO13: GPIO13.3, U2.15 (MTCK/GPIO13/ADC2_CH4)
GPIO14: GPIO14.3, U2.12 (MTMS/GPIO14/ADC2_CH6)
GPIO15: GPIO15.3, U2.23 (MTDO/GPIO15/ADC2_CH3)
GPIO16: GPIO16.3, U2.27 (GPIO16)
GPIO17: GPIO17.3, U2.28 (GPIO17)
GPIO18: GPIO18.3, U2.30 (GPIO18)
GPIO19: GPIO19.3, U2.31 (GPIO19)
GPIO23: GPIO23.3, U2.37 (GPIO23)
GPIO32: GPIO32.3, U2.7 (32K_XP/GPIO32/ADC1_CH4)
GPIO33: GPIO33.3, U2.8 (32K_XN/GPIO33/ADC1_CH5)
GPIO34: GPIO34.3, U2.5 (VDET_1/GPIO34/ADC1_CH6)
GPIO35: GPIO35.3, U2.6 (VDET_2/GPIO35/ADC1_CH7)
GPIO36: GPIO36.3, U2.3 (SENSOR_VP/GPIO36/ADC1_CH0)
GPIO39: GPIO39.3, U2.4 (SENSOR_VN/GPIO39/ADC1_CH3)
I2C0_SCL: I2C0_1.4, I2C0_2.4, I2C0_3.4, I2C0_4.4, R1.1, U2.36 (GPIO22), U3.1 (SCL)
I2C0_SDA: I2C0_1.3, I2C0_2.3, I2C0_3.3, I2C0_4.3, R2.1, U2.33 (GPIO21), U3.3 (SDA)
I2C1_SCL: I2C1_1.4, I2C1_2.4, I2C1_3.4, I2C1_4.4, R3.1, U2.10 (DAC_2/ADC2_CH9/GPIO26)
I2C1_SDA: I2C1_1.3, I2C1_2.3, I2C1_3.3, I2C1_4.3, R4.1, U2.9 (DAC_1/ADC2_CH8/GPIO25)
unnamed: JP1.1 (A), R1.2
unnamed: JP2.1 (A), R2.2
unnamed: JP3.1 (A), R3.2
unnamed: JP4.1 (A), R4.2

Notes on the sheet:
ADC + GPIO
I2C - A
I2C - B
Digital GPIO

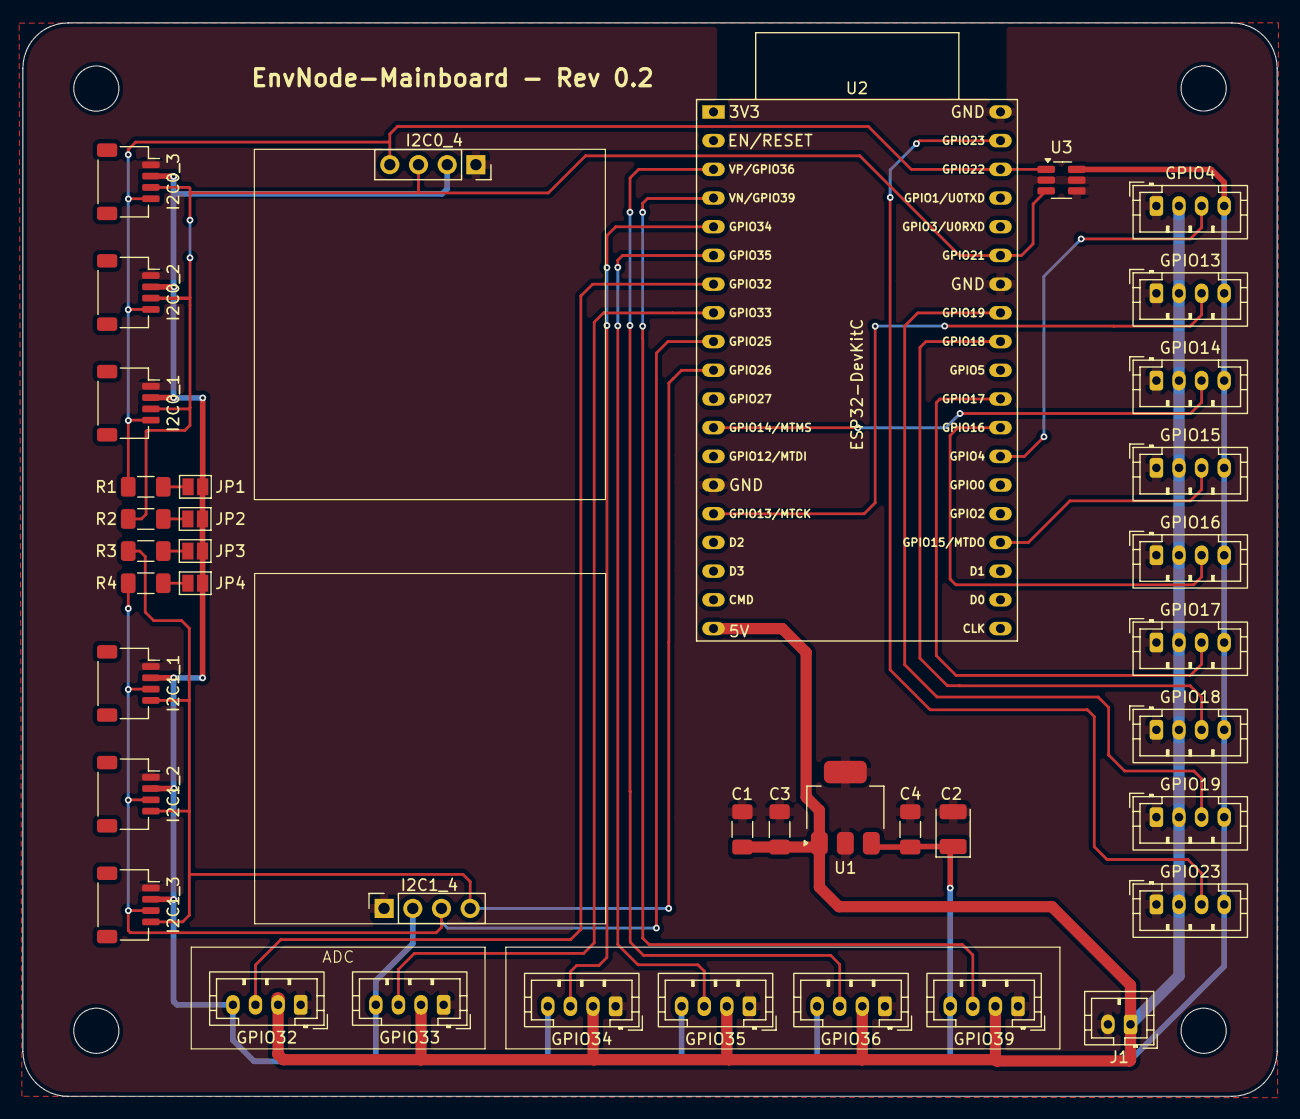
[picture p71: board EnvNode.kicad_pcb from above]

Board: 2 copper layers, 111.0 x 95.0 mm, 39 parts (0 on the bottom side), 26 nets.
