magicamun/EnvNode/hardware/kicad/Revision-0.1/MainBoards/EnvNodeMini/EnvNodeMini.kicad_pcb

## KiCad design hardware/kicad/Revision-0.1/MainBoards/EnvNodeMini/EnvNodeMini.kicad_pcb (2026-08-26)

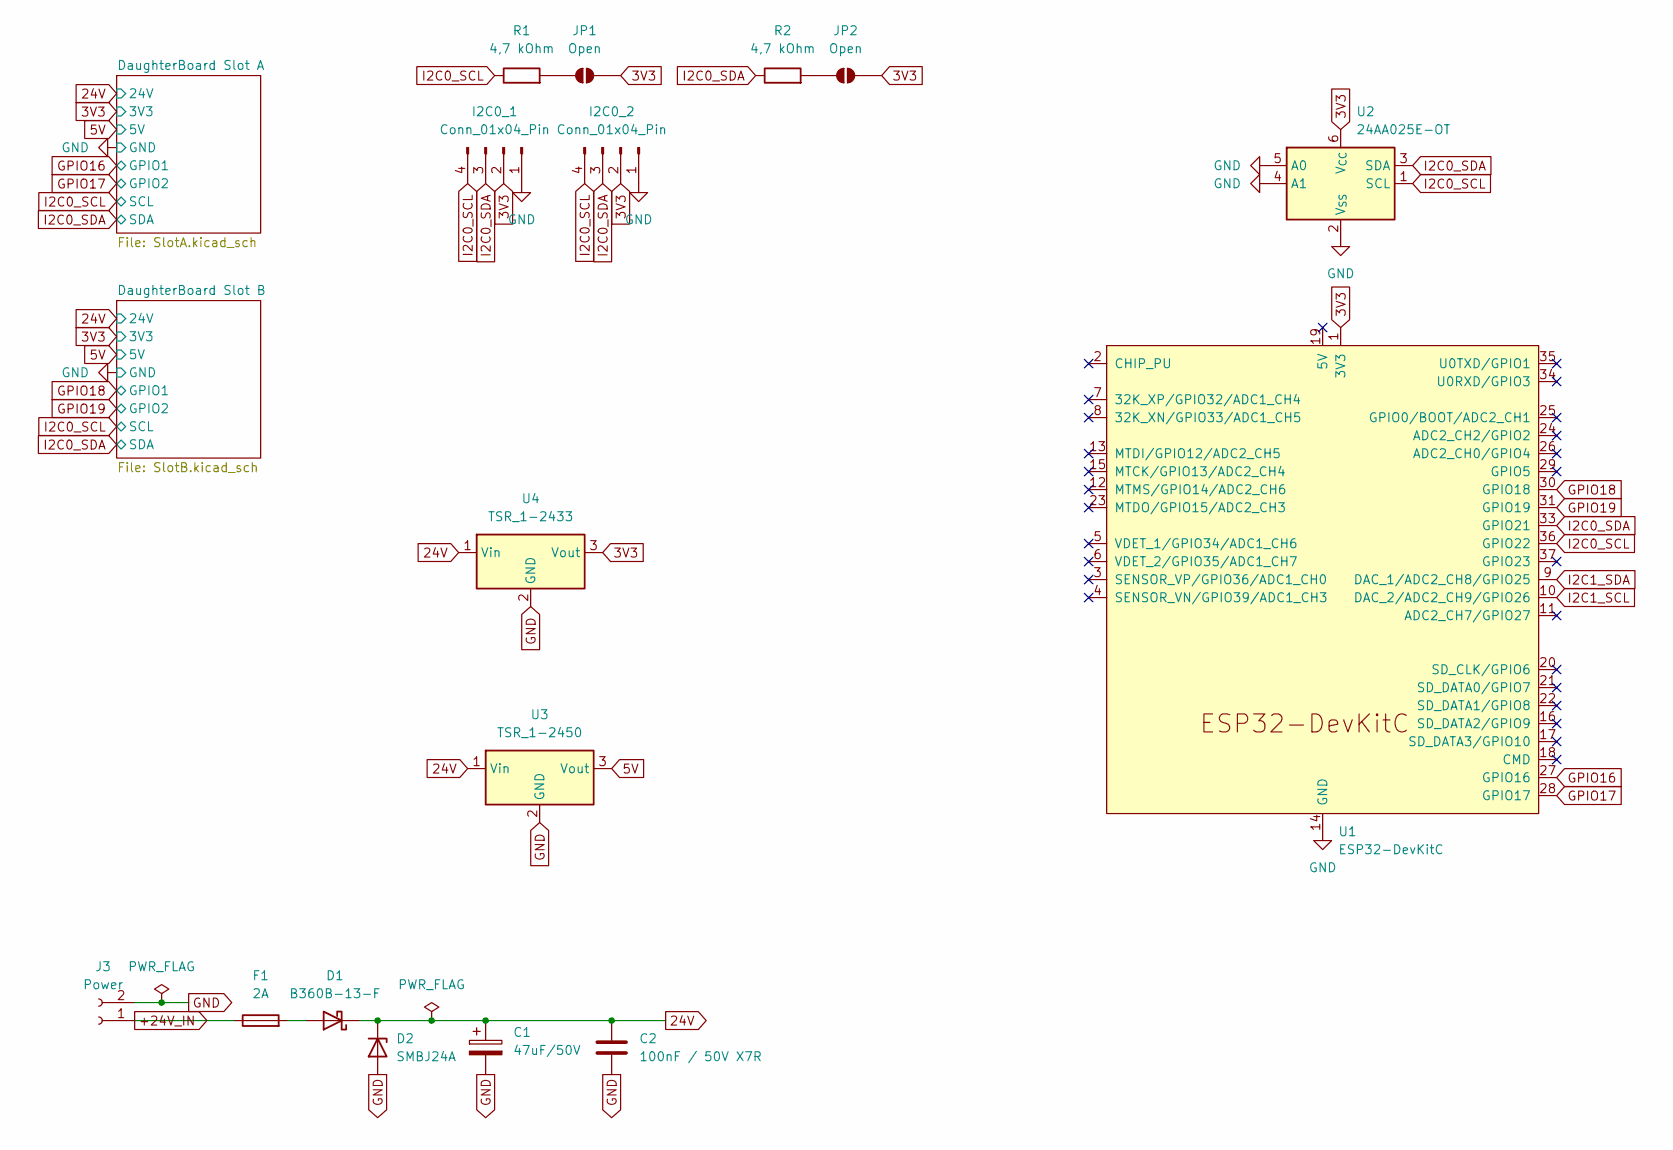
[picture p72: schematic EnvNodeMini.kicad_sch, EnvNode Mini]

Parts:
C1: 47uF/50V; CP_Elec_6.3x7.7
C2: 100nF / 50V X7R; C_1206_3216Metric_Pad1.33x1.80mm_HandSolder
D1: B360B-13-F; D_SMB_Handsoldering
D2: SMBJ24A; D_SMB_Handsoldering
F1: 2A; Fuse_Littelfuse-NANO2-451_453
I2C0_1, I2C0_2: Conn_01x04_Pin; JST_SH_SM04B-SRSS-TB_1x04-1MP_P1.00mm_Horizontal
J3: Power; TerminalBlock_RND_205-00001_1x02_P5.00mm_Horizontal
JP1, JP2: Open; SolderJumper-2_P1.3mm_Open_Pad1.0x1.5mm
R1, R2: 4,7 kOhm; R_1206_3216Metric_Pad1.30x1.75mm_HandSolder
U1: ESP32-DevKitC
U2: 24AA025E-OT; SOT-23-6
U3: TSR_1-2450; Converter_DCDC_TRACO_TSR-1_THT
U4: TSR_1-2433; Converter_DCDC_TRACO_TSR-1_THT

Connections:
3V3: I2C0_1.2, I2C0_2.2, JP1.2 (B), JP2.2 (B), U1.1 (3V3), U2.6 (V_{CC}), U4.3 (Vout); also elsewhere on the board
5V: U3.3 (Vout); also elsewhere on the board
24V: C1.1, C2.1, D1.1 (K), D2.1 (K), U3.1 (Vin), U4.1 (Vin); also elsewhere on the board
+24V_IN: F1.1, J3.1
GND: C1.2, C2.2, D2.2 (A), I2C0_1.1, I2C0_2.1, J3.2, U1.14 (GND), U1.32 (GND), U1.38 (GND), U2.2 (V_{SS}), U2.4 (A1), U2.5 (A0), U3.2 (GND), U4.2 (GND); also elsewhere on the board
GPIO16: U1.27 (GPIO16); also elsewhere on the board
GPIO17: U1.28 (GPIO17); also elsewhere on the board
GPIO18: U1.30 (GPIO18); also elsewhere on the board
GPIO19: U1.31 (GPIO19); also elsewhere on the board
I2C0_SCL: I2C0_1.4, I2C0_2.4, R1.1, U1.36 (GPIO22), U2.1 (SCL); also elsewhere on the board
I2C0_SDA: I2C0_1.3, I2C0_2.3, R2.1, U1.33 (GPIO21), U2.3 (SDA); also elsewhere on the board
I2C1_SCL: U1.10 (DAC_2/ADC2_CH9/GPIO26)
I2C1_SDA: U1.9 (DAC_1/ADC2_CH8/GPIO25)
unnamed: D1.2 (A), F1.2
unnamed: JP1.1 (A), R1.2
unnamed: JP2.1 (A), R2.2

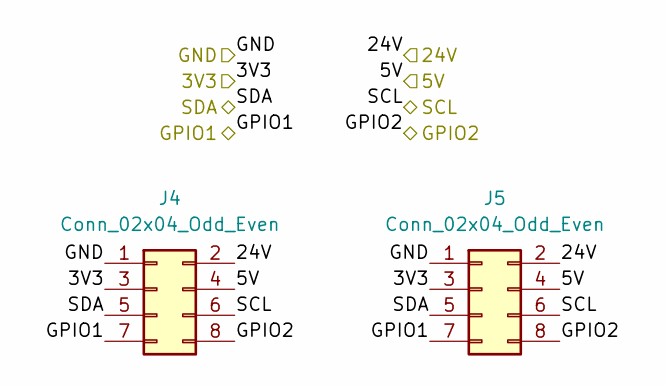
[picture p73: schematic SlotA.kicad_sch]

Parts:
J4, J5: Conn_02x04_Odd_Even; PinSocket_2x04_P2.54mm_Vertical

Connections:
3V3: J4.3, J5.3; also elsewhere on the board
5V: J4.4, J5.4; also elsewhere on the board
24V: J4.2, J5.2; also elsewhere on the board
GND: J4.1, J5.1; also elsewhere on the board
GPIO16: J4.7, J5.7; also elsewhere on the board
GPIO17: J4.8, J5.8; also elsewhere on the board
I2C0_SCL: J4.6, J5.6; also elsewhere on the board
I2C0_SDA: J4.5, J5.5; also elsewhere on the board

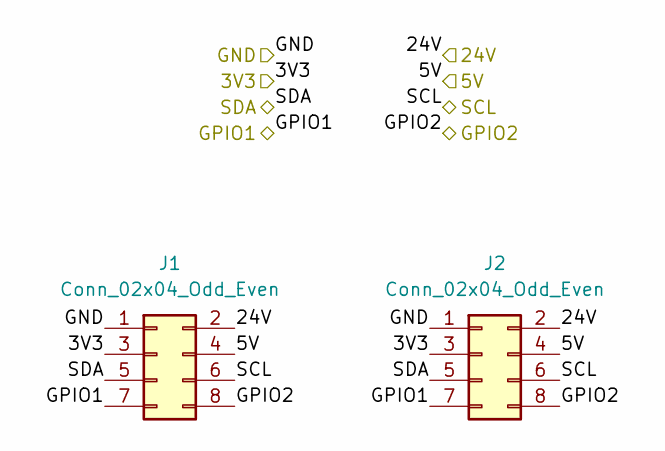
[picture p74: schematic SlotB.kicad_sch]

Parts:
J1, J2: Conn_02x04_Odd_Even; PinSocket_2x04_P2.54mm_Vertical

Connections:
3V3: J1.3, J2.3; also elsewhere on the board
5V: J1.4, J2.4; also elsewhere on the board
24V: J1.2, J2.2; also elsewhere on the board
GND: J1.1, J2.1; also elsewhere on the board
GPIO18: J1.7, J2.7; also elsewhere on the board
GPIO19: J1.8, J2.8; also elsewhere on the board
I2C0_SCL: J1.6, J2.6; also elsewhere on the board
I2C0_SDA: J1.5, J2.5; also elsewhere on the board

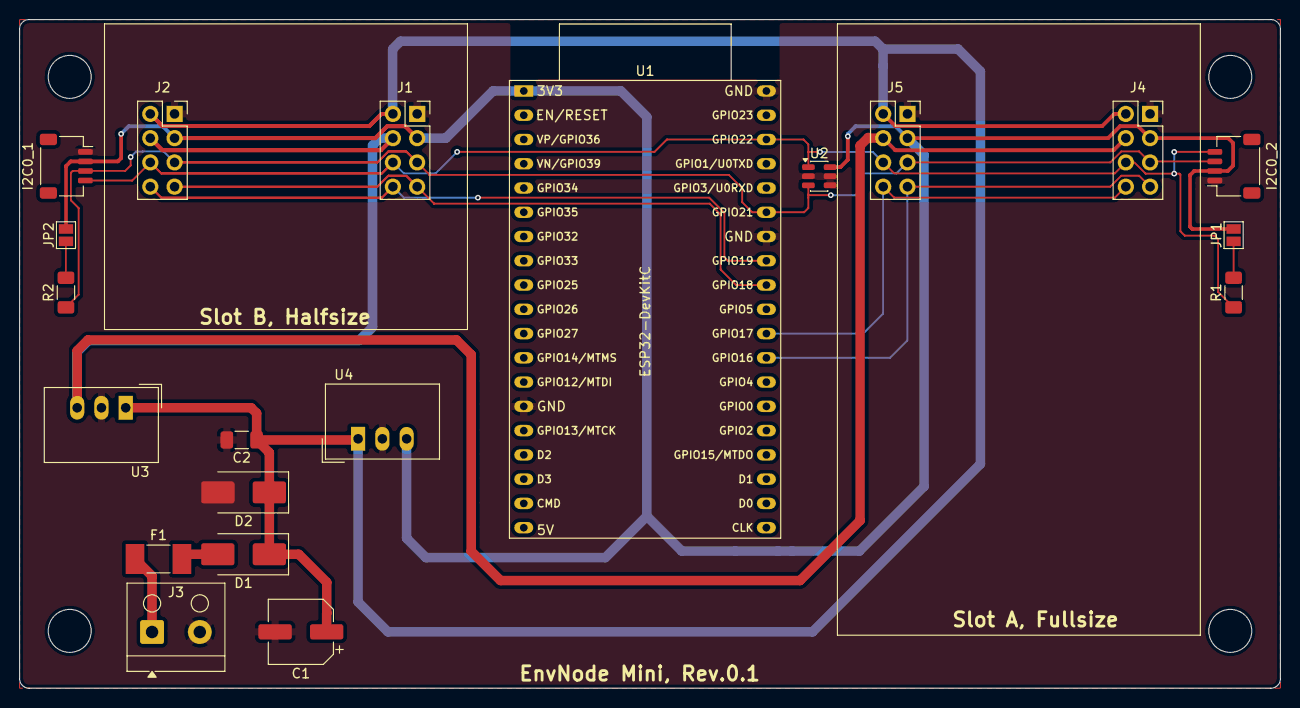
[picture p75: board EnvNodeMini.kicad_pcb from above]

Board: 2 copper layers, 132.0 x 70.0 mm, 20 parts (0 on the bottom side), 14 nets.
