magicamun/EnvNode/hardware/kicad/Revision-0.1/Modules/AnalogInput/AnalogInput.kicad_pcb

## KiCad design hardware/kicad/Revision-0.1/Modules/AnalogInput/AnalogInput.kicad_pcb (2026-08-26)

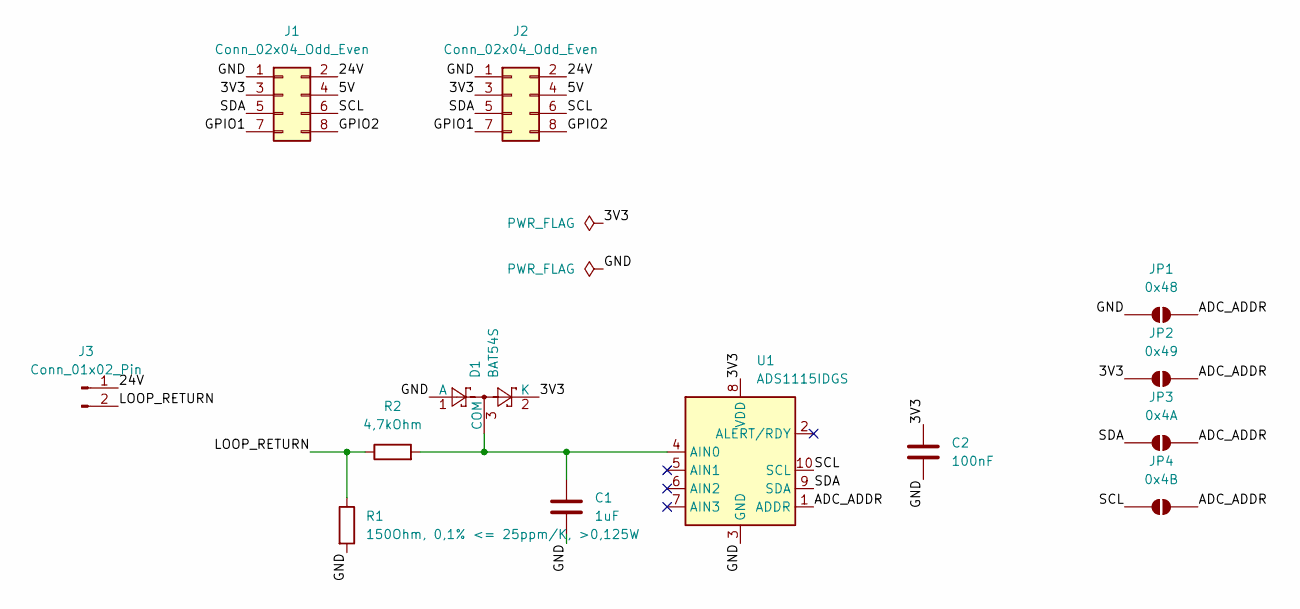
[picture p76: schematic AnalogInput.kicad_sch]

Parts:
C1: 1uF; C_1206_3216Metric_Pad1.33x1.80mm_HandSolder
C2: 100nF; C_1206_3216Metric_Pad1.33x1.80mm_HandSolder
D1: BAT54S; SOT-23
J1, J2: Conn_02x04_Odd_Even; PinSocket_2x04_P2.54mm_Vertical_Bottom
J3: Conn_01x02_Pin; PinSocket_1x02_P2.54mm_Vertical
JP1: 0x48; SolderJumper-2_P1.3mm_Open_Pad1.0x1.5mm
JP2: 0x49; SolderJumper-2_P1.3mm_Open_Pad1.0x1.5mm
JP3: 0x4A; SolderJumper-2_P1.3mm_Open_Pad1.0x1.5mm
JP4: 0x4B; SolderJumper-2_P1.3mm_Open_Pad1.0x1.5mm
R1: 150Ohm, 0,1% <= 25ppm/K, >0,125W; R_Axial_DIN0207_L6.3mm_D2.5mm_P7.62mm_Horizontal
R2: 4,7kOhm; R_1206_3216Metric_Pad1.30x1.75mm_HandSolder
U1: ADS1115IDGS; TSSOP-10_3x3mm_P0.5mm

Connections:
/3V3: C2.1, D1.2 (K), J1.3, J2.3, JP2.1 (A), U1.8 (VDD)
/5V: J1.4, J2.4
/24V: J1.2, J2.2, J3.1
/ADC_ADDR: JP1.2 (B), JP2.2 (B), JP3.2 (B), JP4.2 (B), U1.1 (ADDR)
/GND: C1.2, C2.2, D1.1 (A), J1.1, J2.1, JP1.1 (A), R1.2, U1.3 (GND)
/GPIO1: J1.7, J2.7
/GPIO2: J1.8, J2.8
/LOOP_RETURN: J3.2, R1.1, R2.1
/SCL: J1.6, J2.6, JP4.1 (A), U1.10 (SCL)
/SDA: J1.5, J2.5, JP3.1 (A), U1.9 (SDA)
unnamed: C1.1, D1.3 (COM), R2.2, U1.4 (AIN0)

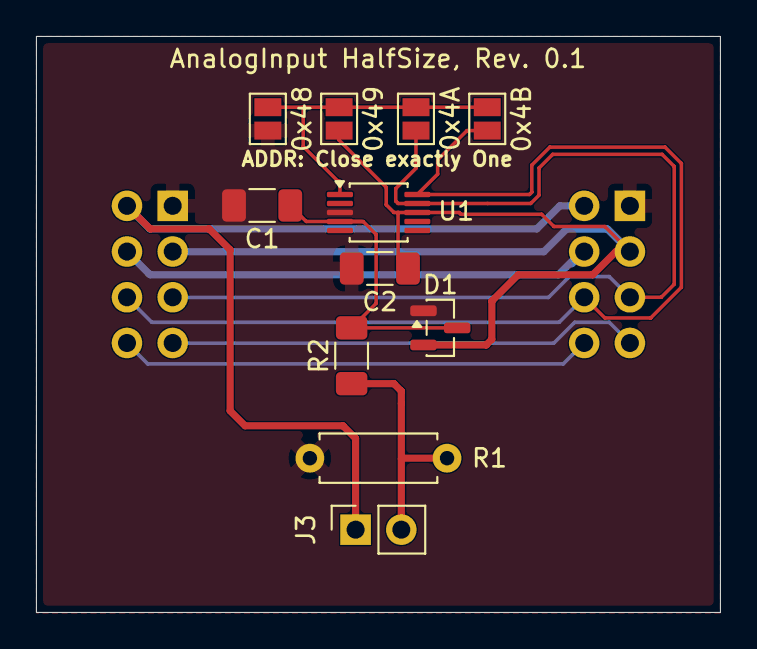
[picture p77: board AnalogInput.kicad_pcb from above]

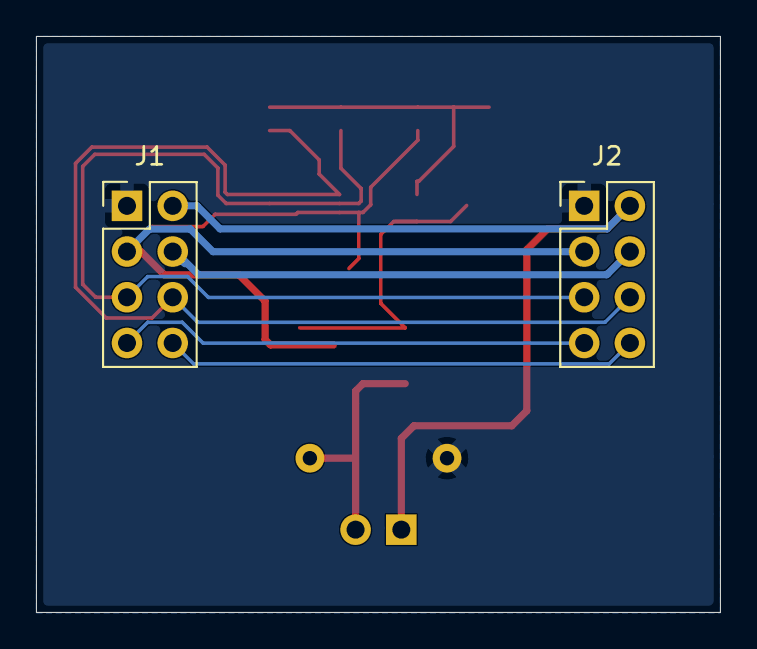
[picture p78: board AnalogInput.kicad_pcb from below]

Board: 2 copper layers, 38.0 x 32.0 mm, 13 parts (2 on the bottom side), 11 nets.
