magicamun/EnvNode/firmware/include/HardwareResources.h

#pragma once

#include <cstddef>
#include <cstdint>

namespace EnvNode {

enum class HardwareInterfaceKind {
    Simulation,
    GPIO,
    I2C,
    OneWire,
    ADC,
    SPI,
    Custom,
};

enum class HardwareResourceKind {
    None,
    GPIO,
    I2C,
};

struct GpioResource {
    explicit GpioResource(uint8_t gpioNumber = 0)
        : number(gpioNumber) {
    }

    uint8_t number;
};

enum class I2CBus : uint8_t {
    I2C0 = 0,
    I2C1 = 1,
};

struct I2CResource {
    I2CResource(I2CBus busNumber = I2CBus::I2C0, uint8_t deviceAddress = 0x76)
        : bus(busNumber)
        , address(deviceAddress) {
    }

    I2CBus bus;
    uint8_t address;
};

struct HardwareResourceAssignment {
    HardwareResourceKind kind = HardwareResourceKind::None;
    GpioResource gpio;
    I2CResource i2c;

    static HardwareResourceAssignment none();
    static HardwareResourceAssignment gpioResource(GpioResource resource);
    static HardwareResourceAssignment i2cResource(I2CResource resource);
};

struct HardwareResourceClaim {
    HardwareResourceClaim(
        bool isActive = false,
        HardwareResourceAssignment resourceAssignment = HardwareResourceAssignment())
        : active(isActive)
        , assignment(resourceAssignment) {
    }

    bool active;
    HardwareResourceAssignment assignment;
};

enum class GpioCapability : uint8_t {
    None = 0,
    DigitalInput = 1U << 0,
    DigitalOutput = 1U << 1,
    Interrupt = 1U << 2,
    InternalPullup = 1U << 3,
    AnalogInput = 1U << 4,
};

constexpr GpioCapability operator|(GpioCapability left, GpioCapability right) {
    return static_cast<GpioCapability>(
        static_cast<uint8_t>(left) | static_cast<uint8_t>(right));
}

constexpr bool hasGpioCapabilities(GpioCapability available, GpioCapability required) {
    return (static_cast<uint8_t>(available) & static_cast<uint8_t>(required))
        == static_cast<uint8_t>(required);
}

struct BoardGpioCapability {
    GpioResource resource;
    const char* displayName;
    GpioCapability capabilities;
};

struct BoardI2CBusCapability {
    I2CBus bus;
    GpioResource sda;
    GpioResource scl;
};

enum class HardwareResourceValidationResult {
    Valid,
    ResourceNotRequired,
    ResourceKindMismatch,
    ResourceDoesNotExist,
    ResourceUnavailable,
    ResourceReserved,
};

class IHardwareResourceConflictValidator {
public:
    virtual ~IHardwareResourceConflictValidator() = default;

    virtual bool conflicts(
        const HardwareResourceAssignment& existing,
        const HardwareResourceAssignment& candidate) const = 0;
};

class BoardCapabilities {
public:
    static const BoardCapabilities& current();

    const BoardGpioCapability* gpio(GpioResource resource) const;
    size_t gpioCount() const;
    const BoardGpioCapability* gpioAt(size_t index) const;
    const BoardI2CBusCapability* i2cBus(I2CBus bus) const;
    size_t i2cBusCount() const;
    const BoardI2CBusCapability* i2cBusAt(size_t index) const;
    HardwareResourceValidationResult validate(
        HardwareInterfaceKind interfaceKind,
        const HardwareResourceAssignment& assignment,
        GpioCapability requiredGpioCapabilities = GpioCapability::None) const;

private:
    BoardCapabilities(const BoardGpioCapability* gpios, size_t gpioCount,
        const BoardI2CBusCapability* i2cBuses, size_t i2cBusCount);

    const BoardGpioCapability* gpios_;
    size_t gpioCount_;
    const BoardI2CBusCapability* i2cBuses_;
    size_t i2cBusCount_;
};

const char* i2cBusName(I2CBus bus);

bool exclusiveHardwareResourceConflict(
    const HardwareResourceAssignment& first,
    const HardwareResourceAssignment& second);

bool validateExclusiveHardwareResourceOccupancy(
    const HardwareResourceClaim* claims,
    size_t claimCount);

const char* hardwareInterfaceKindName(HardwareInterfaceKind kind);

} // namespace EnvNode
