magicamun/EnvNode/firmware/include/ILevelActuator.h

#pragma once

#include "ActuatorLevel.h"
#include "IOnOffActuator.h"

namespace EnvNode {

class ILevelActuator : public IOnOffActuator {
public:
    virtual ActuatorOperationResult setLevel(ActuatorLevel level) = 0;
    virtual ActuatorLevel level() const = 0;
};

} // namespace EnvNode
