magicamun/EnvNode/firmware/src/DisplayConfiguration.cpp

#include "DisplayConfiguration.h"
#include "PropertySourceInput.h"
#include <cstring>
#include <string>
#include <memory>

namespace EnvNode {
namespace {
constexpr size_t MaximumEncodedLength = MaxDisplayEncodedLength;
}

const char* textDisplayTypeName(TextDisplayType type) {
    switch (type) {
    case TextDisplayType::Ssd1309: return "SSD1309 · 128×64";
    case TextDisplayType::Ssd1306: return "SSD1306 · 128×64";
    case TextDisplayType::Sh1106: return "SH1106 · 128×64";
    default: return nullptr;
    }
}
bool parseTextDisplayType(const String& value, TextDisplayType& result) {
    if (value == "0") result = TextDisplayType::Ssd1309;
    else if (value == "1") result = TextDisplayType::Ssd1306;
    else if (value == "2") result = TextDisplayType::Sh1106;
    else return false;
    return true;
}

bool validateTextDisplayConfiguration(const TextDisplayConfiguration& configuration) {
    return textDisplayTypeName(configuration.type) != nullptr
        && BoardCapabilities::current().i2cBus(configuration.bus) != nullptr
        && (configuration.address == 0x3C || configuration.address == 0x3D);
}

bool parseTextDisplayConfiguration(const String& enabled, const String& bus, const String& address,
    TextDisplayConfiguration& result) {
    if ((enabled != "0" && enabled != "1") || (bus != "0" && bus != "1")
        || (address != "60" && address != "61")) return false;
    TextDisplayConfiguration candidate = result;
    candidate.enabled = enabled == "1";
    candidate.bus = bus == "0" ? I2CBus::I2C0 : I2CBus::I2C1;
    candidate.address = address == "60" ? 0x3C : 0x3D;
    if (!validateTextDisplayConfiguration(candidate)) return false;
    result = candidate;
    return true;
}

bool validateDisplayBooleanLabel(const String& text) {
    if (text.length() > MaxDisplayBooleanLabelLength || strlen(text.c_str()) != text.length()) return false;
    for (size_t i = 0; i < text.length(); ++i) {
        const unsigned char character = text[i];
        if (character < 32 || character == 127) return false;
    }
    return true;
}

const char* displayEnumText(const DisplayPage& page, size_t line, size_t source, const char* code) {
    for (const auto& entry : page.enumTranslations) {
        if (entry.line == line && entry.source == source && entry.code == code) return entry.text.c_str();
    }
    return "";
}

static bool validatePage(const DisplayPage& configuration) {
    if (configuration.enumTranslations.size() > MaxDisplayEnumTranslations) return false;
    for (size_t i = 0; i < configuration.enumTranslations.size(); ++i) {
        const auto& entry = configuration.enumTranslations[i];
        if (entry.line >= DisplayLineCount || entry.source >= MaxPropertySourcesPerLine
            || configuration.sources[entry.line][entry.source].isEmpty()
            || entry.code.isEmpty() || entry.code.length() > 32
            || entry.text.isEmpty() || !validateDisplayBooleanLabel(entry.text)) return false;
        for (size_t k = 0; k < entry.code.length(); ++k) {
            const char c = entry.code[k];
            if (!((c >= 'a' && c <= 'z') || (c >= '0' && c <= '9') || c == '_')) return false;
        }
        for (size_t j = 0; j < i; ++j) {
            const auto& previous = configuration.enumTranslations[j];
            if (previous.line == entry.line && previous.source == entry.source && previous.code == entry.code) return false;
        }
    }
    for (size_t line = 0; line < DisplayLineCount; ++line) {
        const String& format = configuration.formats[line];
        if (format.length() > MaxPropertyFormatLength || strlen(format.c_str()) != format.length()) return false;
        size_t count = 0;
        bool gap = false;
        for (size_t index = 0; index < MaxPropertySourcesPerLine; ++index) {
            const String& source = configuration.sources[line][index];
            const auto& labels = configuration.labels[line][index];
            if (!validateDisplayBooleanLabel(labels.trueText) || !validateDisplayBooleanLabel(labels.falseText)) return false;
            if (source.isEmpty()) {
                if (!labels.trueText.isEmpty() || !labels.falseText.isEmpty()) return false;
                gap = true;
                continue;
            }
            PropertySourceInput parsed;
            if (gap || source.length() > MaxPropertySourceLength
                || strlen(source.c_str()) != source.length()
                || !parsePropertySource(source.c_str(), parsed)) return false;
            ++count;
        }
        if (!validatePropertyFormat(format.c_str(), count)) return false;
    }
    return true;
}

bool validateDisplayConfiguration(const DisplayConfiguration& configuration) {
    if (!validatePage(configuration) || !validatePage(configuration.secondPage)) return false;
    for (size_t i = 0; i < 2; ++i)
        if (!validateTextDisplayConfiguration(configuration.output(i)) || configuration.pageAssignment[i] > 1) return false;
    return !(configuration.hardware.enabled && configuration.secondHardware.enabled
        && configuration.hardware.bus == configuration.secondHardware.bus
        && configuration.hardware.address == configuration.secondHardware.address);
}
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
